electrified/rc2014-ym2149/example_template.kibot.yaml

# ATTENTION! THIS ISN'T A FULLY FUNCTIONAL EXAMPLE.
# You should take portions of this example and edit the options to make
# them suitable for your use.
# This file is useful to know all the available options.
# Try using `--quick-start` for a functional example.
kibot:
  version: 1

preflight:
  # Annotate PCB
  # Annotates the PCB according to physical coordinates.
  # This preflight modifies the PCB and schematic, use it only in revision control environments.
  # Used to assign references according to footprint coordinates.
  # The project must be fully annotated first .
  # [dict={}]  Options for the `annotate_pcb` preflight.
  annotate_pcb:
    top_main_axis: y
    top_main_ascending: true
    top_secondary_ascending: true
    top_start: 1
    bottom_main_axis: y
    bottom_main_ascending: true
    bottom_secondary_ascending: true
    bottom_start: 101
    use_position_of: 'footprint'
    grid: 1.0
  # Annotate Power
  # Annotates all power components.
  # This preflight modifies the schematic, use it only in revision control environments.
  # Used to solve ERC problems when using filters that remove power reference numbers .
  # [boolean=false] Enable this preflight.
  annotate_power: true
  # Check Fields
  # Checks to apply to the schematic fields.
  # You can define conditions that must be met by the fields.
  # The checks are applied to every component in the schematic.
  # When an error is hit execution is stopped.
  # One use is to check that all components are suitable for a temperature range.
  # In this case a field must declare the temperature range .
  # [dict|list(dict)=[]] One or more check rules.
  check_fields:
    - field: 'temperature'
      regex: '(-?\d+).+?(?:-?\d+).*'
      numeric_condition: '<='
      numeric_reference: -10
  # Check Zone Fills
  # Zones are filled before doing any operation involving PCB layers.
  # The original PCB remains unchanged. If you need to abort when the zone fill
  # creates significant changes to a layer use the CheckZoneFill internal template .
  # [boolean=false] Enable this preflight.
  check_zone_fills: true
  # Consolidate PCBs
  # Paste one or more PCBs into an existing PCB.
  # This is experimental and isn't intended for generating a PCB to work, just for 3D modeling and/or printing.
  # In the main PCB you just draw text boxes containing a name. Here you map this name to a PCB file name.
  # After executing this preflight the current PCB contains the references PCBs at the text boxes coordinates.
  # Only the top left corner of the text box is relevant.
  # An example can be found [here](https://github.com/INTI-CMNB/KiBot/tree/dev/docs/samples/Consolidate_PCBs)
  # .
  # [dict|list(dict)=[]] One or more PCBs to include.
  consolidate_pcbs: true
  # Draw Fancy Stackup
  # Draw the PCB stackup. Needs KiCad 7 or newer.
  # To specify the position and size of the drawing you can use two methods.
  # You can specify it using the *pos_x*, *pos_y*, *width* and *layer* options.
  # But you can also create a group called *kibot_fancy_stackup*. If you don't know how to
  # create a group consult :ref:`create_group`. After running this preflight the rectangle
  # will contain the stackup.
  # Note that the height is not determined by the group height, but by the number
  # of layers and spacing between layers. .
  # [boolean|dict=false] Use a boolean for simple cases or fine-tune its behavior.
  draw_fancy_stackup: true
  # Draw Stackup
  # Draw the PCB stackup. Needs KiCad 7 or newer.
  # To specify the position and size of the drawing you can use two methods.
  # You can specify it using the *pos_x*, *pos_y*, *width*, *height* and *layer* options.
  # But you can also create a group called *kibot_stackup*. If you don't know how to
  # create a group consult :ref:`create_group`. After running this preflight the rectangle
  # will contain the stackup .
  # [boolean|dict=false] Use a boolean for simple cases or fine-tune its behavior.
  draw_stackup: true
  # DRC
  # Runs the DRC (Distance Rules Check) to ensure we have a valid PCB.
  # You need a valid *fp-lib-table* installed. If not KiBot will try to temporarily install the template.
  # This is a replacement for the *run_drc* preflight that needs KiCad 8 or newer.
  # GUI exclusions and schematic parity are supported .
  # [boolean|dict=false] Use a boolean for simple cases or fine-tune its behavior.
  drc: true
  # ERC
  # Runs the ERC (Electrical Rules Check). To ensure the schematic is electrically correct.
  # You need a valid *sym-lib-table* installed. If not KiBot will try to temporarily install the template.
  # This is a replacement for the *run_erc* preflight that needs KiCad 8 or newer .
  # [boolean|dict=false] Use a boolean for simple cases or fine-tune its behavior.
  erc: true
  # ERC Warnings (**Deprecated**)
  # Option for `run_erc`. ERC warnings are considered errors.
  # Use the `warnings_as_errors` option from `run_erc`/`erc` instead .
  # [boolean=false] Enable this preflight.
  erc_warnings: false
  # Fill Zones
  # Fill all zones again and save the PCB .
  # [boolean=false] Enable this preflight.
  fill_zones: true
  # Filters
  # A list of entries to filter out ERC/DRC messages when using *run_erc*/*run_drc*.
  # Avoid using it with the new *erc* and *drc* preflights.
  # Note that ignored errors will become KiBot warnings (i.e. `(W058) ...`).
  # To farther ignore these warnings use the `filters` option in the `global` section .
  # [list(dict)=[]] One or more filters.
  filters:
    - filter: 'Filter description'
      error: '10'
      regex: 'Regular expression to match'
  # Ignore Unconnected (**Deprecated**)
  # Option for `run_drc`. Ignores the unconnected nets. Useful if you didn't finish the routing.
  # It will also ignore KiCad 6 warnings when using `run_drc`.
  # Use the `ignore_unconnected` option from `run_drc`/`drc` instead .
  # [boolean=false] Enable this preflight.
  ignore_unconnected: false
  # Include Table
  # Draws a table in the PCB from data in a CSV generated by an output. Needs KiCad 7 or newer.
  # To specify the position and size of the drawing create a group called *kibot_table_X* where
  # X should match the name of the output. If you don't know how to create a group consult
  # :ref:`create_group`. Consult the `group_name` option for details.
  # After running this preflight the rectangle will contain the table with the same name.
  # Only the width of the table is important, the height will be adjusted.
  # Important: This preflight assumes that a separated KiBot run generated the outputs
  # needed for the tables .
  # [boolean|dict=false] Use a boolean for simple cases or fine-tune its behavior.
  include_table: true
  # PCB Replace (**Deprecated**)
  # Replaces tags in the PCB. I.e. to insert the git hash or last revision date.
  # This is useful for KiCad 5, use `set_text_variables` when using KiCad 6.
  # This preflight modifies the PCB. Even when a back-up is done use it carefully .
  # [dict={}] Options for the `pcb_replace` preflight.
  pcb_replace:
    date_command: 'git log -1 --format="%as" -- "$KIBOT_PCB_NAME"'
    replace_tags:
      - tag: '@git_hash@'
        command: 'git log -1 --format="%h" "$KIBOT_PCB_NAME"'
        before: 'Git hash: <'
        after: '>'
  # Run DRC (**Deprecated for KiCad 8**)
  # Runs the DRC (Distance Rules Check) to ensure we have a valid PCB.
  # For KiCad 8 use *drc*
  # The report file name is controlled by the global output pattern (%i=drc %x=txt).
  # Note that the KiCad 6+ *Test for parity between PCB and schematic* option is not supported.
  # If you need to check the parity use the `update_xml` preflight.
  # KiCad 6 introduced `warnings` they are currently counted be the `unconnected` counter of KiBot.
  # This will change in the future.
  # If you use DRC exclusions please consult the `drc_exclusions_workaround` global option .
  # [boolean|dict=false] Use a boolean for simple cases or fine-tune its behavior.
  run_drc: true
  # Run ERC (**Deprecated for KiCad 8**)
  # Runs the ERC (Electrical Rules Check).
  # For KiCad 8 use *erc*
  # To ensure the schematic is electrically correct.
  # The report file name is controlled by the global output pattern (%i=erc %x=txt) .
  # [boolean|dict=false] Use a boolean for simple cases or fine-tune its behavior.
  run_erc: true
  # SCH Replace (**Deprecated**)
  # Replaces tags in the schematic. I.e. to insert the git hash or last revision date.
  # This is useful for KiCad 5, use `set_text_variables` when using KiCad 6.
  # This preflight modifies the schematics. Even when a back-up is done use it carefully .
  # [dict={}] Options for the `sch_replace` preflight.
  sch_replace:
    date_command: 'git log -1 --format="%as" -- "$KIBOT_SCH_NAME"'
    replace_tags:
      - tag: '@git_hash@'
        command: 'git log -1 --format="%h" "$KIBOT_SCH_NAME"'
        before: 'Git hash: <'
        after: '>'
  # Set Text Variables
  # Defines KiCad 6+ variables.
  # They are expanded using `${VARIABLE}`, and stored in the project file.
  # This preflight replaces `pcb_replace` and `sch_replace` when using KiCad 6 or newer.
  # The KiCad project file is modified.
  # Warning:     don't use `-s all` or this preflight will be skipped .
  # [dict|list(dict)=[]] One or more variable definition.
  set_text_variables:
    - name: 'git_hash'
      command: 'git log -1 --format="%h" "$KIBOT_PCB_NAME"'
      before: 'Git hash: <'
      after: '>'
  # Update Footprint
  # Updates footprints from the libs, you must provide one or more
  # references to be updated. This is useful to replace logos using freshly created versions .
  # [string|list(string)=''] {comma_sep} One or more component references.
  update_footprint: QR1,QR2
  # Update PCB Characteristics
  # Update the information in the Board Characteristics.
  # Starting with KiCad 7 you can paste a block containing board information using
  # Place* -> *Add Board Characteristics*. But this information is static, so if
  # you modify anything related to it the block will be obsolete.
  # This preflight tries to refresh the information .
  # [boolean=false] Enable this preflight.
  update_pcb_characteristics: true
  # Update QR
  # Update the QR codes.
  # Complements the `qr_lib` output.
  # The KiCad 6 files and the KiCad 5 PCB needs manual update, generating a new library isn't enough .
  # [boolean=false] Enable this preflight.
  update_qr: true
  # Update Stackup
  # Update the information in the Stackup Table.
  # Starting with KiCad 7 you can paste a block containing board information using
  # *Place* -> *Stackup Table*. But this information is static, so if
  # you modify anything related to it the block will be obsolete.
  # This preflight tries to refresh the information .
  # [boolean=false] Enable this preflight.
  update_stackup: true
  # Update XML
  # Update the XML version of the BoM (Bill of Materials).
  # To ensure our generated BoM is up to date.
  # Note that this isn't needed when using the internal BoM generator (`bom`).
  # You can compare the PCB and schematic netlists using it (KiCad 6 and 7 only) .
  # [boolean|dict=false] Use a boolean for simple cases or fine-tune its behavior.
  update_xml: true

outputs:
  # Blender Export:
  # Also renders the PCB with high-quality.
  # Needs KiCad 6 or newer.
  # This output is complex to setup and needs very big dependencies.
  # Please be patient when using it.
  # You need Blender with the pcb2blender plug-in installed.
  # Visit: [pcb2blender](https://github.com/30350n/pcb2blender).
  # You can just generate the exported PCB if no output is specified.
  # You can also export the PCB and render it at the same time
  - name: 'blender_export_example'
    comment: 'Exports the PCB in various 3D file formats.'
    type: 'blender_export'
    dir: 'Example/blender_export_dir'
    options:
      # [boolean=true] Add a default light when none specified.
      # The default light is located at (-size*3.33, size*3.33, size*5) where size is max(width, height) of the PCB
      add_default_light: true
      # [number=1.1] Value to multiply the Z axis coordinate after computing the automatically generated camera.
      # Used to avoid collision of the camera and the object
      auto_camera_z_axis_factor: 1.1
      # [dict={}] Options for the camera.
      # If none specified KiBot will create a suitable camera.
      # If no position is specified for the camera KiBot will look for a suitable position
      camera:
        # [number=-1] Minimum distance for objects to the camera. Any object closer than this distance won't be visible.
        # Only positive values have effect. A negative value has a special meaning.
        # For a camera with defined position, a negative value means to use Blender defaults (i.e. 0.1 m).
        # For cameras without position KiBot will ask Blender to compute its position and the use a clip
        # distance that is 1/10th of the Z distance
        clip_start: -1
        # [string=''] Name for the camera
        name: ''
        # [number|string=0] X position [m]. You can use `width`, `height` and `size` for PCB dimensions
        pos_x: 0
        # [number|string=0] Y position [m]. You can use `width`, `height` and `size` for PCB dimensions
        pos_y: 0
        # [number|string=0] Z position [m]. You can use `width`, `height` and `size` for PCB dimensions
        pos_z: 0
        # [string='perspective'] [perspective,orthographic,panoramic] Type of camera
        type: 'perspective'
      # [string=''] Default value for the `file_id` in the `point_of_view` options.
      # Use something like '_%03d' for animations
      default_file_id: ''
      # [boolean=false] When using the automatically generated camera and multiple points of view this option computes the camera
      # position just once. Suitable for videos
      fixed_auto_camera: false
      # [dict|list(dict)] Options for the light/s
      light:
        # [number=0] How powerful is the light. Using 0 for POINT and SUN KiBot will try to use something useful
        - energy: 0
          # [string=''] Name for the light
          name: ''
          # [number|string=0] X position [m]. You can use `width`, `height` and `size` for PCB dimensions
          pos_x: 0
          # [number|string=0] Y position [m]. You can use `width`, `height` and `size` for PCB dimensions
          pos_y: 0
          # [number|string=0] Z position [m]. You can use `width`, `height` and `size` for PCB dimensions
          pos_z: 0
          # [string='POINT'] [POINT,SUN,SPOT,HEMI,AREA] Type of light. SUN lights will illuminate more evenly
          type: 'POINT'
      # [dict|list(dict)] Outputs to generate in the same run
      outputs:
        # [string=''] Subdirectory for this output
        - dir: ''
          # [string='%f-%i%I%v.%x'] Name for the generated file (%i='3D_blender_$VIEW' %x=VARIABLE).
          # The extension is selected from the type. Affected by global options
          output: '%f-%i%I%v.%x'
          # [string='render'] [fbx,obj,x3d,gltf,stl,ply,blender,render] The format for the output.
          # The `render` type will generate a PNG image of the render result.
          # `fbx` is Kaydara's Filmbox, 'obj' is the Wavefront, 'x3d' is the new ISO/IEC standard
          # that replaced VRML, `gltf` is the standardized GL format, `stl` is the 3D printing
          # format, 'ply' is Polygon File Format (Stanford).
          # Note that some formats includes the light and camera and others are just the 3D model
          # (i.e. STL and PLY)
          type: 'render'
      # [string|dict={}] Options to export the PCB to Blender.
      # You can also specify the name of the output that generates the PCB3D file.
      # See the `PCB2Blender_2_1`, `PCB2Blender_2_7` and `PCB2Blender_2_1_haschtl` templates
      pcb3d:
        # [string|list(string)='_null'] Name of the filter to mark components as not fitted.
        # Is a short-cut to use for simple cases where a variant is an overkill.
        # Can be used to fine-tune a variant for a particular output that needs extra filtering done before the
        # variant
        dnf_filter: '_null'
        # [boolean=true] Downloads missing 3D models from KiCad git.
        # Only applies to models in KISYS3DMOD and KICAD6_3DMODEL_DIR.
        # They are downloaded to a temporal directory and discarded.
        # If you want to cache the downloaded files specify a directory using the
        # KIBOT_3D_MODELS environment variable
        download: true
        # [boolean=true] In addition to try to download the 3D models from KiCad git also try to get
        # them from LCSC database. In order to work you'll need to provide the LCSC
        # part number. The field containing the LCSC part number is defined by the
        # `field_lcsc_part` global variable
        download_lcsc: true
        # [string|list(string)='_null'] Name of the filter to exclude components from processing.
        # Is a short-cut to use for simple cases where a variant is an overkill.
        # Can be used to fine-tune a variant for a particular output that needs extra filtering done before the
        # variant
        exclude_filter: '_null'
        # [list(string)=[]] List of components to highlight. Ranges like *R5-R10* are supported
        highlight: []
        # [boolean=false] Highlight over the component (not under)
        highlight_on_top: false
        # [number=1.5] [0,1000] How much the highlight extends around the component [mm]
        highlight_padding: 1.5
        # [string='https://gitlab.com/kicad/libraries/kicad-packages3D/-/raw/master/'] Base URL for the KiCad 3D models
        kicad_3d_url: 'https://gitlab.com/kicad/libraries/kicad-packages3D/-/raw/master/'
        # [string=''] Text added to the end of the download URL.
        # Can be used to pass variables to the GET request, i.e. ?VAR1=VAL1&VAR2=VAL2
        kicad_3d_url_suffix: ''
        # [boolean=false] Used to exclude 3D models for components with 'virtual' attribute
        no_virtual: false
        # [string='%f-%i%I%v.%x'] Name for the generated PCB3D file (%i='blender_export' %x='pcb3d'). Affected by global options
        output: '%f-%i%I%v.%x'
        # [string|list(string)='_null'] Name of the filter to transform fields before applying other filters.
        # Is a short-cut to use for simple cases where a variant is an overkill.
        # Can be used to fine-tune a variant for a particular output that needs extra filtering done before the
        # variant
        pre_transform: '_null'
        # [list(string)|string='all'] [none,all,*] List of components to draw, can be also a string for `none` or `all`.
        # Ranges like *R5-R10* are supported.
        # Unlike the `pcbdraw` output, the default is `all`
        show_components: 'all'
        # [boolean=true] Solder the THT pads with heatsink fabrication attribute
        solder_join_on_heatsink: true
        # [boolean=true] Add solder paste only for the populated components.
        # Populated components are the ones listed in `show_components`
        solder_paste_for_populated: true
        # [string=''] Board variant to apply
        variant: ''
        # [string='2.7'] [2.1,2.1_haschtl,2.7] Variant of the format used
        version: '2.7'
      # [dict={}] Options to configure how Blender imports the PCB.
      # The default values are good for most cases
      pcb_import:
        # [boolean=true] Center the PCB at the coordinates origin
        center: true
        # [boolean=true] Import the components
        components: true
        # [boolean=true] Separate the sub-PCBs in separated 3D models
        cut_boards: true
        # [boolean=true] Create good looking materials
        enhance_materials: true
        # [boolean=true] Reuse materials
        merge_materials: true
        # [string='SMART'] [NONE,SMART,ALL] The plug-in can add nice looking solder joints.
        # This option controls if we add it for none, all or only for THT/SMD pads with solder paste
        solder_joints: 'SMART'
        # [boolean=true] Move the sub-PCBs to their relative position
        stack_boards: true
        # [number=1016.0] [508,2032] Texture density in dots per inch
        texture_dpi: 1016.0
      # [dict|list(dict)] How the object is viewed by the camera
      point_of_view:
        # [string=''] String to differentiate the name of this point of view.
        # When empty we use the `default_file_id` or the `view`
        - file_id: ''
          # [number=0] Angle to rotate the board in the X axis, positive is clockwise [degrees]
          rotate_x: 0
          # [number=0] Angle to rotate the board in the Y axis, positive is clockwise [degrees]
          rotate_y: 0
          # [number=0] Angle to rotate the board in the Z axis, positive is clockwise [degrees]
          rotate_z: 0
          # [number=1] [1,1000] Generate this amount of steps using the rotation angles as increments.
          # Use a value of 1 (default) to interpret the angles as absolute.
          # Used for animations. You should define the `default_file_id` to something like
          # '_%03d' to get the animation frames
          steps: 1
          # [string='top'] [top,bottom,front,rear,right,left,z,Z,y,Y,x,X] Point of view.
          # Compatible with `render_3d`
          view: 'top'
      # [dict={}] Controls how the render is done for the `render` output type
      render_options:
        # [boolean=false] When enabled the image will be post-processed to remove the empty space around the image.
        # In this mode the `background2` is changed to be the same as `background1`
        auto_crop: false
        # [string='#66667F'] First color for the background gradient
        background1: '#66667F'
        # [string='#CCCCE5'] Second color for the background gradient
        background2: '#CCCCE5'
        # `height` is an alias for `resolution_y`
        # [boolean=false] Used to disable the render denoiser on old hardware, or when the functionality isn't compiled.
        # Note that the impact in quality is huge, you should increase the amount of samples 10 times
        no_denoiser: false
        # [number=1280] Width of the image
        resolution_x: 1280
        # [number=720] Height of the image
        resolution_y: 720
        # [number=10] How many samples we create. Each sample is a raytracing render.
        # Use 1 for a raw preview, 10 for a draft and 100 or more for the final render
        samples: 10
        # [boolean=false] Make the background transparent
        transparent_background: false
        # `width` is an alias for `resolution_x`
  # BoardView:
  # This format allows simple pads and connections navigation, mainly for circuit debug.
  # The output can be loaded using Open Board View (https://openboardview.org/)
  - name: 'boardview_example'
    comment: 'Exports the PCB in board view format.'
    type: 'boardview'
    dir: 'Example/boardview_dir'
    options:
      # [string|list(string)='_null'] Name of the filter to mark components as not fitted.
      # Is a short-cut to use for simple cases where a variant is an overkill.
      # Can be used to fine-tune a variant for a particular output that needs extra filtering done before the
      # variant
      dnf_filter: '_null'
      # [string|list(string)='_null'] Name of the filter to exclude components from processing.
      # Is a short-cut to use for simple cases where a variant is an overkill.
      # Can be used to fine-tune a variant for a particular output that needs extra filtering done before the
      # variant
      exclude_filter: '_null'
      # [string='BRD'] [BRD,BVR,OBDATA] Format used for the generated file. The BVR file format is bigger but keeps
      # more information, like alphanumeric pin names.
      # OBDATA is the OpenBoardData format. You can include the manufacturer part number defining the global
      # `field_part_number` variable. Excluded and not fitted components are marked with `-` status
      format: 'BRD'
      # [string='%f-%i%I%v.%x'] Filename for the output (%i=boardview, %x=brd/brv). Affected by global options
      output: '%f-%i%I%v.%x'
      # [string|list(string)='_null'] Name of the filter to transform fields before applying other filters.
      # Is a short-cut to use for simple cases where a variant is an overkill.
      # Can be used to fine-tune a variant for a particular output that needs extra filtering done before the
      # variant
      pre_transform: '_null'
      # [boolean=true] Sort components by reference. Disable this option to get a file closer to what
      # kicad-boardview generates
      sorted: true
      # [string=''] Board variant to apply.
      # Used for sub-PCBs
      variant: ''
  # BoM (Bill of Materials):
  # This output can generate XYRS files (pick and place files).
  # You can import the options used in the KiCad internal BoM, consult :ref:`bom_kicad_options`.
  # Is compatible with KiBoM, but doesn't need to update the XML netlist because the components
  # are loaded from the schematic.
  # Important differences with KiBoM output:
  # - All options are in the main `options` section, not in `conf` subsection.
  # - The `Component` column is named `Row` and works just like any other column.
  - name: 'bom_example'
    comment: 'Used to generate the BoM in CSV, HTML, TSV, TXT, XML or XLSX format using the internal BoM.'
    type: 'bom'
    dir: 'Example/bom_dir'
    options:
      # [list(dict)=[]] Add components from other projects.
      # You can use CSV files, the first row must contain the names of the fields.
      # The `Reference` and `Value` are mandatory, in most cases `Part` is also needed.
      # The `Part` column should contain the name/type of the component. This is important for
      # passive components (R, L, C, etc.). If this information isn't available consider
      # configuring the grouping to exclude the `Part`
      aggregate:
        # [string=','] Delimiter used for CSV files
        - delimiter: ','
          # [string=''] Name of the schematic to aggregate
          file: 'another_schematic.kicad_sch'
          # [string=''] Name to identify this source. If empty we use the name of the schematic
          name: ''
          # [number=1] Number of boards to build (components multiplier). Use negative to subtract
          number: 1
          # [string=''] A prefix to add to all the references from this project
          ref_id: ''
      # [boolean=true] Always use positive values for the footprint rotation
      angle_positive: true
      # [boolean=false] Use negative X coordinates for footprints on bottom layer (for XYRS)
      bottom_negative_x: false
      # [list(dict)|list(string)=computed for your project] List of columns to display.
      # One entry can be just the name of the field (a string).
      # If you want to import the columns used in KiCad internal BoM tool add an entry `_kicad_bom_fields`,
      # this will be replaced by the list from KiCad.
      # In addition to all user defined fields you have various special columns, consult :ref:`bom_columns`
      columns:
        # [string=''] Used as explanation for this column. The XLSX output uses it
        - comment: ''
          # [string=''] Name of the field to use for this column.
          # Use `_field_lcsc_part` to get the value defined in the global options
          field: 'Row'
          # [list(dict)|list(string)|string=''] List of fields to join to this column
          join:
            # [string=''] {no_case} Name of the field
            - field: 'Voltage'
              # [string=''] Text to use instead of a field. This option is incompatible with the `field` option.
              # Any space to separate it should be added in the text.
              # Use \n for newline and \t for tab
              text: ''
              # [string=''] Text to add after the field content. Will be added only if the field isn't empty.
              # Any space to separate it should be added in the text.
              # Use \n for newline and \t for tab
              text_after: ''
              # [string=''] Text to add before the field content. Will be added only if the field isn't empty.
              # Any space to separate it should be added in the text.
              # Use \n for newline and \t for tab
              text_before: ''
          # [number=0] Used to group columns. The XLSX output uses it to collapse columns
          level: 0
          # [string=''] Name to display in the header. The field is used when empty
          name: 'Line'
      # [list(list(string))] A series of values which are considered to be equivalent for the part name.
      # Each entry is a list of equivalen names. Example: ['c', 'c_small', 'cap' ]
      # will ensure the equivalent capacitor symbols can be grouped together.
      # If empty the following aliases are used:
      # - ['r', 'r_small', 'res', 'resistor']
      # - ['l', 'l_small', 'inductor']
      # - ['c', 'c_small', 'cap', 'capacitor']
      # - ['sw', 'switch']
      # - ['zener', 'zenersmall']
      # - ['d', 'diode', 'd_small']
      component_aliases: [['r', 'r_small', 'res', 'resistor'], ['l', 'l_small', 'inductor'], ['c', 'c_small', 'cap', 'capacitor'], ['sw', 'switch'], ['zener', 'zenersmall'], ['d', 'diode', 'd_small']]
      # [list(dict)|list(string)=[]] List of columns to add to the global section of the cost.
      # Can be just the name of the field
      cost_extra_columns:
        # [string=''] Used as explanation for this column. The XLSX output uses it
        - comment: ''
          # [string=''] Name of the field to use for this column.
          # Use `_field_lcsc_part` to get the value defined in the global options
          field: 'Row'
          # [list(dict)|list(string)|string=''] List of fields to join to this column
          join:
            # [string=''] {no_case} Name of the field
            - field: 'Voltage'
              # [string=''] Text to use instead of a field. This option is incompatible with the `field` option.
              # Any space to separate it should be added in the text.
              # Use \n for newline and \t for tab
              text: ''
              # [string=''] Text to add after the field content. Will be added only if the field isn't empty.
              # Any space to separate it should be added in the text.
              # Use \n for newline and \t for tab
              text_after: ''
              # [string=''] Text to add before the field content. Will be added only if the field isn't empty.
              # Any space to separate it should be added in the text.
              # Use \n for newline and \t for tab
              text_before: ''
          # [number=0] Used to group columns. The XLSX output uses it to collapse columns
          level: 0
          # [string=''] Name to display in the header. The field is used when empty
          name: 'Line'
      # [boolean=false] Show the stats about how many of the components are SMD/THT. You must provide the PCB
      count_smd_tht: false
      # [dict={}] Options for the CSV, TXT and TSV formats
      csv:
        # [boolean=false] Hide the header line (names of the columns)
        hide_header: false
        # [boolean=false] Hide project information
        hide_pcb_info: false
        # [boolean=false] Hide statistics information
        hide_stats_info: false
        # [boolean=true] Don't remove line breaks in field values
        keep_line_breaks: true
        # [boolean=true] Don't remove tabs in field values
        keep_tabs: true
        # [boolean=false] Enclose all values using double quotes
        quote_all: false
        # [string=','] CSV Separator. TXT and TSV always use tab as delimiter.
        # Only one character can be specified
        separator: ','
        # [string='"'] Character used to delimite strings
        string_delimiter: '"'
      # [string|list(string)=[]] {comma_sep} Include this distributors list. Default is all the available
      distributors: []
      # [string|list(string)='_kibom_dnc_CONFIG_FIELD'] Name of the filter to mark components as 'Do Not Change'.
      # The default filter marks components with a DNC value or DNC in the Config field.
      # This option is for simple cases, consider using a full variant for complex cases
      dnc_filter: '_kibom_dnc_CONFIG_FIELD'
      # [string|list(string)='_kibom_dnf_CONFIG_FIELD'] Name of the filter to mark components as 'Do Not Fit'.
      # The default filter marks components with a DNF value or DNF in the Config field.
      # This option is for simple cases, consider using a full variant for complex cases
      dnf_filter: '_kibom_dnf_CONFIG_FIELD'
      # [string|list(string)='_mechanical'] Name of the filter to exclude components from BoM processing.
      # The default filter (built-in filter '_mechanical') excludes test points, fiducial marks, mounting holes, etc.
      # Please consult the built-in filters explanation to fully understand what is excluded by default.
      # This option is for simple cases, consider using a full variant for complex cases
      exclude_filter: '_mechanical'
      # [boolean=false] Exclude components marked with *Exclude from BOM* in the PCB.
      # This is a KiCad 6 option
      exclude_marked_in_pcb: false
      # [boolean=true] Exclude components marked with *Exclude from bill of materials* in the schematic.
      # This is a KiCad 6 option
      exclude_marked_in_sch: true
      # [boolean=true] Expand KiCad 6 text variables after applying all filters and variants.
      # This is done using a **_expand_text_vars** filter.
      # If you need to customize the filter, or apply it before, you can disable this option and
      # add a custom filter to the filter chain
      expand_text_vars: true
      # [string='config'] {no_case} Field name used for internal filters (not for variants)
      fit_field: 'config'
      # [string|list(string)='no,yes'] {comma_sep} {L:2} Values for the `Footprint Populate` column
      footprint_populate_values: 'no,yes'
      # [string|list(string)='SMD,THT,VIRTUAL'] {comma_sep} {L:3} Values for the `Footprint Type` column
      footprint_type_values: 'SMD,THT,VIRTUAL'
      # [string='Auto'] [HTML,CSV,TXT,TSV,XML,XLSX,HRTXT,KICAD,Auto] format for the BoM.
      # `Auto` defaults to CSV or a guess according to the options.
      # HRTXT stands for Human Readable TeXT.
      # KICAD is used to get the options from KiCad project. In KiCad you can configure CSV like options
      format: 'Auto'
      # [boolean=true] Connectors with the same footprints will be grouped together, independent of the name of the connector
      group_connectors: true
      # [list(string)] {no_case} List of fields used for sorting individual components into groups.
      # Components which match (comparing *all* fields) will be grouped together.
      # Field names are case-insensitive.
      # For empty fields the behavior is defined by the `group_fields_fallbacks`, `merge_blank_fields` and
      # `merge_both_blank` options.
      # Note that for resistors, capacitors and inductors the _Value_ field is parsed and qualifiers, like
      # tolerance, are discarded. Please use a separated field and disable `merge_blank_fields` if this
      # information is important. You can also disable `parse_value`.
      # When using `_kicad_bom_fields` in the `columns` you should use `[]` for this value, so the fields
      # selected in KiCad are used.
      # If empty: ['Part', 'Part Lib', 'Value', 'Footprint', 'Footprint Lib',
      #            'Voltage', 'Tolerance', 'Current', 'Power'] is used
      group_fields: ['part', 'part lib', 'value', 'footprint', 'footprint lib', 'voltage', 'tolerance', 'current', 'power']
      # [list(string)=[]] {no_case} List of fields to be used when the fields in `group_fields` are empty.
      # The first field in this list is the fallback for the first in `group_fields`, and so on
      group_fields_fallbacks: []
      # [boolean=false] Enable it to group fitted and not fitted components together. This is how KiCad's internal BoM behaves
      group_not_fitted: false
      # [dict={}] Options for the HRTXT formats
      hrtxt:
        # [string='-'] Separator between the header and the data
        header_sep: '-'
        # [boolean=false] Hide the header line (names of the columns)
        hide_header: false
        # [boolean=false] Hide project information
        hide_pcb_info: false
        # [boolean=false] Hide statistics information
        hide_stats_info: false
        # [string='left'] [left,right,center] Text justification
        justify: 'left'
        # [string='I'] Column Separator
        separator: 'I'
      # [dict={}] Options for the HTML format
      html:
        # [boolean=true] Use colors to show the field type
        col_colors: true
        # [string=''] {no_case} Column with links to the datasheet
        datasheet_as_link: ''
        # [string|list(string)=''] {no_case} Column/s containing Digi-Key part numbers, will be linked to web page
        digikey_link: ''
        # [string|list(string)=''] Information to put after the title and before the pcb and stats info
        extra_info: ''
        # [boolean=true] Generate a separated section for DNF (Do Not Fit) components
        generate_dnf: true
        # [boolean=false] Hide project information
        hide_pcb_info: false
        # [boolean=false] Hide statistics information
        hide_stats_info: false
        # [boolean=true] Use a color for empty cells. Applies only when `col_colors` is `true`
        highlight_empty: true
        # [boolean|string|list(string)=''] {no_case} Column/s containing LCSC part numbers, will be linked to web page.
        # Use **true** to copy the value indicated by the `field_lcsc_part` global option
        lcsc_link: ''
        # [string|boolean=''] PNG/SVG file to use as logo, use false to remove.
        # Note that when using an SVG this is first converted to a PNG using `logo_width`
        logo: ''
        # [number=370] Used when the logo is an SVG image. This width is used to render the SVG image
        logo_width: 370
        # [string|list(string)=''] {no_case} Column/s containing Mouser part numbers, will be linked to web page
        mouser_link: ''
        # [list(dict)=[]] Used to highlight rows using filters. Rows that match a filter can be colored.
        # Note that these rows won't have colored columns
        row_colors:
          # [string='#FF8080'] Color used for this category
          - color: '#FF8080'
            # [string=''] A description for this color, must be filled
            description: "Components that can't be replaced"
            # [string|list(string)='_none'] Name of the filter to match.
            # Be careful because this filter should be coherent with the grouping fields.
            # KiBot will assume that all the components grouped in the same group will
            # return the same value when applying this filter
            filter: '_none'
        # [string='modern-blue'] Page style. Internal styles: modern-blue, modern-green, modern-red and classic.
        # Or you can provide a CSS file name. Please use .css as file extension.
        style: 'modern-blue'
        # [string='KiBot Bill of Materials'] BoM title
        title: 'KiBot Bill of Materials'
      # [boolean=true] Exclude DNF (Do Not Fit) components
      ignore_dnf: true
      # [boolean=true] Component quantities are always expressed as integers. Using the ceil() function
      int_qtys: true
      # [string='global'] [global,yes,no] What we do with the KiCad DNP flag.
      # `global` means we apply the `kicad_dnp_applied` global option.
      # `yes` means we always remove DNP components.
      # `no` means we ignore the DNP flag and let filters do its work
      kicad_dnp_applied: 'global'
      # [boolean=true] Component groups with blank fields will be merged into the most compatible group, where possible
      merge_blank_fields: true
      # [boolean=true] When creating groups two components with empty/missing field will be interpreted as with the same value
      merge_both_blank: true
      # [list(string)=computed for your project] {no_case} List of fields where we tolerate conflicts.
      # Use it to avoid undesired warnings.
      # By default the field indicated in `fit_field`, the field used for variants and
      # the field `part` are excluded
      no_conflict: ['Config', 'Part']
      # [string|list(string)=[]] {comma_sep} Exclude this distributors list.
      # They are removed after computing `distributors`
      no_distributors: []
      # [boolean=false] When normalizing values use the locale decimal point
      normalize_locale: false
      # [boolean=false] Try to normalize the R, L and C values, producing uniform units and prefixes
      normalize_values: false
      # [number=1] Number of boards to build (components multiplier)
      number: 1
      # [string='%f-%i%I%v.%x'] filename for the output (%i=bom). The extension depends on the selected format.
      # In the case of the **KICAD** format the extension comes from the name you selected in KiCad's
      # internal BoM. Affected by global options
      output: '%f-%i%I%v.%x'
      # [boolean=true] Parse the `Value` field so things like *1k* and *1000* are interpreted as equal.
      # Note that this implies that *1k 1%* is the same as *1k 5%*. If you really need to group using the
      # extra information split it in separated fields, add the fields to `group_fields` and disable
      # `merge_blank_fields`
      parse_value: true
      # [string|list(string)='_null'] Name of the filter to transform fields before applying other filters.
      # This option is for simple cases, consider using a full variant for complex cases
      pre_transform: '_null'
      # [string=''] A prefix to add to all the references from this project. Used for multiple projects
      ref_id: ''
      # [string='-'] Separator used for ranges in the list of references. Used when `use_alt` is enabled.
      # Ignored when using the KICAD format
      ref_range_separator: '-'
      # [string=' '] Separator used for the list of references. Ignored when using the KICAD format
      ref_separator: ' '
      # [number=4] Number of digits for mantissa part of coordinates ('Footprint X', 'Footprint Y', 'Footprint X-Size',
      # 'Footprint Y-Size' and 'Footprint Rot' columns) (0 is auto)
      right_digits: 4
      # [boolean=true] Sort in ascending order
      sort_ascending: true
      # [string|list(string)='Reference'] {no_case} Field or fields used for the `field` `sort_style`
      sort_field: 'Reference'
      # [string='type_value'] [type_value,type_value_ref,ref,kicad_bom,field] Sorting criteria.
      # - type_value: component kind (reference prefix), then by value
      # - type_value_ref: like *type_value* but use the reference when we don't have a value
      # - ref: by reference
      # - kicad_bom: according to the options of the KiCad BoM tool
      # - field: using the `sort_field` field/s
      sort_style: 'type_value'
      # [boolean=false] Generate the `Source BoM` column using the reference ID instead of the project name
      source_by_id: false
      # [string='millimeters'] [millimeters,inches,mils] Units used for the positions ('Footprint X', 'Footprint Y', 'Footprint X-Size' and
      # 'Footprint Y-Size' columns).
      # Affected by global options
      units: 'millimeters'
      # [boolean=false] Print grouped references in the alternate compressed style eg: R1-R7,R18.
      # Ignored when using the KICAD format
      use_alt: false
      # [boolean=true] Use the auxiliary axis as origin for coordinates (KiCad default) (for XYRS)
      use_aux_axis_as_origin: true
      # `use_ref_ranges` is an alias for `use_alt`
      # [string='_kibom_simple'] Board variant, used to determine which components are output to the BoM.
      # The `_kibom_simple` variant is a KiBoM variant without any filters and it provides some basic
      # compatibility with KiBoM. Note that this output has default filters that behaves like KiBoM.
      # The combination between the default for this option and the defaults for the filters provides
      # a behavior that mimics KiBoM default behavior
      variant: '_kibom_simple'
      # [dict={}] Options for the XLSX format
      xlsx:
        # [boolean=true] Use colors to show the field type
        col_colors: true
        # [string=''] {no_case} Column with links to the datasheet
        datasheet_as_link: ''
        # [string|list(string)=''] {no_case} Column/s containing Digi-Key part numbers, will be linked to web page
        digikey_link: ''
        # [string|list(string)=''] Information to put after the title and before the pcb and stats info
        extra_info: ''
        # [boolean=true] Generate a separated section for DNF (Do Not Fit) components
        generate_dnf: true
        # [boolean=false] Hide project information
        hide_pcb_info: false
        # [boolean=false] Hide statistics information
        hide_stats_info: false
        # [boolean=true] Use a color for empty cells. Applies only when `col_colors` is `true`
        highlight_empty: true
        # [boolean=false] Enable KiCost worksheet creation.
        # Note: an example of how to use it on CI/CD can be found [here](https://github.com/set-soft/kicost_ci_test)
        kicost: false
        # [string|list(string)=''] {comma_sep} List of KiCost APIs to disable
        kicost_api_disable: ''
        # [string|list(string)=''] {comma_sep} List of KiCost APIs to enable
        kicost_api_enable: ''
        # [string=''] KiCost configuration file. It contains the keys for the different distributors APIs.
        # The regular KiCost config is used when empty.
        # Important for CI/CD environments: avoid exposing your API secrets!
        # To understand how to achieve this, and also how to make use of the cache please visit the
        # [kicost_ci_test](https://github.com/set-soft/kicost_ci_test) repo
        kicost_config: ''
        # [boolean=false] Used to add a column with the distributor's description. So you can check this is the right component
        kicost_dist_desc: false
        # [boolean|string|list(string)=''] {no_case} Column/s containing LCSC part numbers, will be linked to web page.
        # Use **true** to copy the value indicated by the `field_lcsc_part` global option
        lcsc_link: ''
        # [string|boolean=''] PNG/SVG file to use as logo, use false to remove.
        # Note that when using an SVG this is first converted to a PNG using `logo_width`
        logo: ''
        # [number=2] Scaling factor for the logo. Note that this value isn't honored by all spreadsheet software
        logo_scale: 2
        # [number=370] Used when the logo is an SVG image. This width is used to render the SVG image
        logo_width: 370
        # [number=60] [20,999] Maximum column width (characters)
        max_col_width: 60
        # [string|list(string)=''] {no_case} Column/s containing Mouser part numbers, will be linked to web page
        mouser_link: ''
        # [list(dict)=[]] Used to highlight rows using filters. Rows that match a filter can be colored.
        # Note that these rows won't have colored columns
        row_colors:
          # [string='#FF8080'] Color used for this category
          - color: '#FF8080'
            # [string=''] A description for this color, must be filled
            description: "Components that can't be replaced"
            # [string|list(string)='_none'] Name of the filter to match.
            # Be careful because this filter should be coherent with the grouping fields.
            # KiBot will assume that all the components grouped in the same group will
            # return the same value when applying this filter
            filter: '_none'
        # [boolean=false] Enable Specs worksheet creation. Contains specifications for the components.
        # Works with only some KiCost APIs
        specs: false
        # [list(dict)|list(string)=[]] Which columns are included in the Specs worksheet. Use `References` for the
        # references, 'Row' for the order and 'Sep' to separate groups at the same level. By default all are included.
        # Column names are distributor specific, the following aren't: '_desc', '_value', '_tolerance', '_footprint',
        # '_power', '_current', '_voltage', '_frequency', '_temp_coeff', '_manf', '_size'.
        # Note that an empty list means all available specs, use `specs` options to disable it
        specs_columns:
          # [string=''] Used as explanation for this column. The XLSX output uses it
          - comment: ''
            # [string=''] Name of the field to use for this column.
            # Use `_field_lcsc_part` to get the value defined in the global options
            field: 'Row'
            # [list(dict)|list(string)|string=''] List of fields to join to this column
            join:
              # [string=''] {no_case} Name of the field
              - field: 'Voltage'
                # [string=''] Text to use instead of a field. This option is incompatible with the `field` option.
                # Any space to separate it should be added in the text.
                # Use \n for newline and \t for tab
                text: ''
                # [string=''] Text to add after the field content. Will be added only if the field isn't empty.
                # Any space to separate it should be added in the text.
                # Use \n for newline and \t for tab
                text_after: ''
                # [string=''] Text to add before the field content. Will be added only if the field isn't empty.
                # Any space to separate it should be added in the text.
                # Use \n for newline and \t for tab
                text_before: ''
            # [number=0] Used to group columns. The XLSX output uses it to collapse columns
            level: 0
            # [string=''] Name to display in the header. The field is used when empty
            name: 'Line'
        # [string='modern-blue'] Head style: modern-blue, modern-green, modern-red and classic
        style: 'modern-blue'
        # [string='KiBot Bill of Materials'] BoM title
        title: 'KiBot Bill of Materials'
  # Archiver (files compressor):
  # This is used to generate groups of files in compressed file format.
  - name: 'compress_example'
    comment: 'Generates a compressed file containing output files.'
    type: 'compress'
    dir: 'Example/compress_dir'
    options:
      # [string='auto'] [auto,stored,deflated,bzip2,lzma] Compression algorithm. Use auto to let KiBot select a suitable one
      compression: 'auto'
      # [list(dict)=[]] Which files will be included
      files:
        # [string=''] Destination directory inside the archive, empty means the same of the file
        - dest: ''
          # [string='.*'] A regular expression that source files must match
          filter: '.*'
          # [boolean=false] Use the current working directory instead of the dir specified by `-d`
          from_cwd: false
          # [string=''] Collect files from the selected output.
          # When used the `source` option is ignored
          from_output: ''
          # [boolean=false] Use the current directory specified by the output instead of the dir specified by `-d`.
          # Note that it only applies when using `from_output` and no `dest` is specified.
          # It has more prescedence than `from_cwd`
          from_output_dir: false
          # [string='*'] File names to add, wildcards allowed. Use ** for recursive match.
          # By default this pattern is applied to the output dir specified with `-d` command line option.
          # See the `from_cwd` and `from_output_dir` options
          source: '*'
      # [boolean=true] Store the file pointed by symlinks, not the symlink
      follow_links: true
      # [string='ZIP'] [ZIP,TAR,RAR] Output file format
      format: 'ZIP'
      # [boolean=false] Move the files to the archive. In other words: remove the files after adding them to the archive
      move_files: false
      # [string='%f-%i%I%v.%x'] Name for the generated archive (%i=name of the output %x=according to format). Affected by global options
      output: '%f-%i%I%v.%x'
      # `remove_files` is an alias for `move_files`
      # [boolean=false] Skip outputs with `run_by_default: false`
      skip_not_run: false
  # Files copier:
  # Useful when an external tool is used to compress the output directory.
  # Note that you can use the `compress` output to create archives
  - name: 'copy_files_example'
    comment: 'Used to copy files to the output directory.'
    type: 'copy_files'
    dir: 'Example/copy_files_dir'
    options:
      # [string|list(string)='_null'] Name of the filter to mark components as not fitted.
      # Is a short-cut to use for simple cases where a variant is an overkill.
      # Can be used to fine-tune a variant for a particular output that needs extra filtering done before the
      # variant
      dnf_filter: '_null'
      # [boolean=true] Downloads missing 3D models from KiCad git.
      # Only applies to models in KISYS3DMOD and KICAD6_3DMODEL_DIR.
      # They are downloaded to a temporal directory and discarded.
      # If you want to cache the downloaded files specify a directory using the
      # KIBOT_3D_MODELS environment variable
      download: true
      # [boolean=true] In addition to try to download the 3D models from KiCad git also try to get
      # them from LCSC database. In order to work you'll need to provide the LCSC
      # part number. The field containing the LCSC part number is defined by the
      # `field_lcsc_part` global variable
      download_lcsc: true
      # [string|list(string)='_null'] Name of the filter to exclude components from processing.
      # Is a short-cut to use for simple cases where a variant is an overkill.
      # Can be used to fine-tune a variant for a particular output that needs extra filtering done before the
      # variant
      exclude_filter: '_null'
      # [list(dict)=[]] Which files will be included
      files:
        # [string=''] Destination directory inside the output dir, empty means the same of the file
        # relative to the source directory.
        # Note that when you specify a name here files are copied to this destination
        # without creating subdirs. The `project` mode is an exception.
        # For the `3d_models` type you can use DIR+ to create subdirs under DIR
        - dest: ''
          # [string='.*'] A regular expression that source files must match.
          # Not used for the `project` mode
          filter: '.*'
          # [boolean=false] Only usable for the `3d_models` mode.
          # Save a PCB copy modified to use the copied 3D models.
          # You don't need to specify it for `project` mode
          save_pcb: false
          # [string='*'] For the `files` and `out_files` mode this is th file names to add,
          # wildcards allowed. Use ** for recursive match.
          # For the `output` mode this is the name of the output.
          # For the `3d_models` is a pattern to match the name of the 3D models extracted from the PCB.
          # Not used for the `project` mode
          source: '*'
          # [string='files'] [files,out_files,output,3d_models,project] From where do we get the files to be copied.
          # - `files`: files relative to the current working directory.
          # - `out_files`: files relative to output dir specified with `-d` command line option.
          # - `output`: files generated by the output specified by `source`.
          # - `3d_models`: 3D models used in the project.
          # - `project`: schematic, PCB, footprints, symbols, 3D models and project files (KiCad 6+)
          source_type: 'files'
      # [boolean=true] Store the file pointed by symlinks, not the symlink
      follow_links: true
      # [string='https://gitlab.com/kicad/libraries/kicad-packages3D/-/raw/master/'] Base URL for the KiCad 3D models
      kicad_3d_url: 'https://gitlab.com/kicad/libraries/kicad-packages3D/-/raw/master/'
      # [string=''] Text added to the end of the download URL.
      # Can be used to pass variables to the GET request, i.e. ?VAR1=VAL1&VAR2=VAL2
      kicad_3d_url_suffix: ''
      # [boolean=false] Create symlinks instead of copying files
      link_no_copy: false
      # [boolean=false] Used to exclude 3D models for components with 'virtual' attribute
      no_virtual: false
      # [string|list(string)='_null'] Name of the filter to transform fields before applying other filters.
      # Is a short-cut to use for simple cases where a variant is an overkill.
      # Can be used to fine-tune a variant for a particular output that needs extra filtering done before the
      # variant
      pre_transform: '_null'
      # [string=''] Board variant to apply
      variant: ''
  # Diff:
  # Recursive git submodules aren't supported (submodules inside submodules)
  - name: 'diff_example'
    comment: 'Generates a PDF with the differences between two PCBs or schematics.'
    type: 'diff'
    dir: 'Example/diff_dir'
    options:
      # [boolean=false] When enabled we create a symlink to the output file with a name that contains the
      # git hashes involved in the comparison. If you plan to compress the output don't
      # forget to disable the `follow_links` option
      add_link_id: false
      # [boolean=false] Always fail if the old/new file doesn't exist. Currently we don't fail if they are from a repo.
      # So if you refer to a repo point where the file wasn't created KiBot will use an empty file.
      # Enabling this option KiBot will report an error
      always_fail_if_missing: false
      # [string=''] Directory to cache the intermediate files. Leave it blank to disable the cache
      cache_dir: ''
      # [string='#00FF00'] Color used for the added stuff in the '2color' mode
      color_added: '#00FF00'
      # [string='#FF0000'] Color used for the removed stuff in the '2color' mode
      color_removed: '#FF0000'
      # [boolean=false] Modifies the behavior of `add_link_id` to create a copy of the file instead of a
      # symlink. Useful for some Windows setups
      copy_instead_of_link: false
      # [string='red_green'] [red_green,stats,2color] In the `red_green` mode added stuff is green and red when removed.
      # The `stats` mode is used to measure the amount of difference. In this mode all
      # changes are red, but you can abort if the difference is bigger than certain threshold.
      # The '2color' mode is like 'red_green', but you can customize the colors
      diff_mode: 'red_green'
      # [string|list(string)='_null'] Name of the filter to mark components as not fitted.
      # Is a short-cut to use for simple cases where a variant is an overkill.
      # Can be used to fine-tune a variant for a particular output that needs extra filtering done before the
      # variant
      dnf_filter: '_null'
      # [string|list(string)='_null'] Name of the filter to exclude components from processing.
      # Is a short-cut to use for simple cases where a variant is an overkill.
      # Can be used to fine-tune a variant for a particular output that needs extra filtering done before the
      # variant
      exclude_filter: '_null'
      # [boolean=false] When `old_type` and/or `new_type` are `git` KiBot will checkout the indicated point.
      # Before doing it KiBot will stash any change. Under some circumstances git could fail
      # to do a checkout, even after stashing, this option can workaround the problem.
      # Note that using it you could potentially lose modified files. For more information
      # read https://stackoverflow.com/questions/1248029/git-pull-error-entry-foo-not-uptodate-cannot-merge
      force_checkout: false
      # [number=5] [0,100] Color tolerance (fuzzyness) for the `stats` mode
      fuzz: 5
      # [string|list(string)] The file you want to compare. Leave it blank for the current PCB/SCH.
      # A list is accepted only for the `multivar` type. Consult the `old` option for more information
      new: ''
      # [string='current'] [git,file,output,multivar,current] How to interpret the `new` name. Use `git` for a git hash, branch, etc.
      # Use `current` for the currently loaded PCB/Schematic.
      # Use `file` for a file name. Use `output` to specify the name of a `pcb_variant`/`sch_variant` output.
      # Use `multivar` to compare a set of variants, in this mode `new` is the list of outputs for the variants.
      # This is an extension of the `output` mode.
      # If `old` is also `multivar` then it becomes the reference, otherwise we compare using pairs of variants
      new_type: 'current'
      # [string='HEAD'] Reference file. When using git use `HEAD` to refer to the last commit.
      # Use `HEAD~` to refer the previous to the last commit.
      # As `HEAD` is for the whole repo you can use `KIBOT_LAST-n` to make
      # reference to the changes in the PCB/SCH. The `n` value is how many
      # changes in the history you want to go back. A 0 is the same as `HEAD`,
      # a 1 means the last time the PCB/SCH was changed, etc.
      # Use `KIBOT_TAG-n` to search for the last tag skipping `n` tags.
      # Important: when using the `checkout` GitHub action you just get the
      # last commit. To clone the full repo use `fetch-depth: '0'`
      old: 'HEAD'
      # [string='git'] [git,file,output,multivar] How to interpret the `old` name. Use `git` for a git hash, branch, etc.
      # Use `file` for a file name. Use `output` to specify the name of a `pcb_variant`/`sch_variant` output.
      # Use `multivar` to specify a reference file when `new_type` is also `multivar`
      old_type: 'git'
      # [boolean=false] Only include the pages with differences in the output PDF.
      # Note that when no differences are found we get a page saying *No diff*
      only_different: false
      # [boolean=false] Compare only the main schematic page (root page).
      # Warning: Make sure this page is the page **1** of your schematic
      only_first_sch_page: false
      # [string='%f-%i%I%v.%x'] Filename for the output (%i=diff_pcb/diff_sch, %x=pdf). Affected by global options
      output: '%f-%i%I%v.%x'
      # [boolean=true] Compare the PCB, otherwise compare the schematic
      pcb: true
      # [string|list(string)='_null'] Name of the filter to transform fields before applying other filters.
      # Is a short-cut to use for simple cases where a variant is an overkill.
      # Can be used to fine-tune a variant for a particular output that needs extra filtering done before the
      # variant
      pre_transform: '_null'
      # [number=0] [0,1000000] Error threshold for the `stats` mode, 0 is no error. When specified a
      # difference bigger than the indicated value will make the diff fail.
      # KiBot will return error level 29 and the diff generation will be aborted
      threshold: 0
      # [boolean=false] When creating the link name of an output file related to a variant use the variant
      # `file_id` instead of its name
      use_file_id: false
      # [string=''] Board variant to apply
      variant: ''
      # [string='global'] [global,fill,unfill,none] How to handle PCB zones. The default is *global* and means that we
      # fill zones if the *check_zone_fills* preflight is enabled. The *fill* option always forces
      # a refill, *unfill* forces a zone removal and *none* lets the zones unchanged.
      # Be careful with the cache when changing this setting
      zones: 'global'
    layers: all
  # Datasheets downloader:
  - name: 'download_datasheets_example'
    comment: 'Downloads the datasheets for the project'
    type: 'download_datasheets'
    dir: 'Example/download_datasheets_dir'
    options:
      # [boolean=false] Use the reference to classify the components in different sub-dirs.
      # In this way C7 will go into a Capacitors sub-dir, R3 into Resistors, etc
      classify: false
      # [string_dict={}] Extra reference associations used to classify the references.
      # They are pairs `Reference prefix` -> `Sub-dir`
      classify_extra: {}
      # [boolean=false] Include the DNF components
      dnf: false
      # [string|list(string)='_null'] Name of the filter to mark components as not fitted.
      # Is a short-cut to use for simple cases where a variant is an overkill.
      # Can be used to fine-tune a variant for a particular output that needs extra filtering done before the
      # variant
      dnf_filter: '_null'
      # [string|list(string)='_null'] Name of the filter to exclude components from processing.
      # Is a short-cut to use for simple cases where a variant is an overkill.
      # Can be used to fine-tune a variant for a particular output that needs extra filtering done before the
      # variant
      exclude_filter: '_null'
      # [string='Datasheet'] Name of the field containing the URL
      field: 'Datasheet'
      # [boolean=true] Instead of download things we already downloaded use symlinks
      link_repeated: true
      # [string='${VALUE}.pdf'] Name used for the downloaded datasheet.
      # `${FIELD}` will be replaced by the FIELD content
      output: '${VALUE}.pdf'
      # [string|list(string)='_null'] Name of the filter to transform fields before applying other filters.
      # Is a short-cut to use for simple cases where a variant is an overkill.
      # Can be used to fine-tune a variant for a particular output that needs extra filtering done before the
      # variant
      pre_transform: '_null'
      # [boolean=false] Download URLs that we already downloaded.
      # It only makes sense if the `output` field makes their output different
      repeated: false
      # [string=''] Board variant to apply
      variant: ''
  # DXF (Drawing Exchange Format):
  # This output is what you get from the File/Plot menu in pcbnew.
  # Important: If you use custom fonts and/or colors please consult the `resources_dir` global variable.
  - name: 'dxf_example'
    comment: 'Exports the PCB to 2D mechanical EDA tools (like AutoCAD).'
    type: 'dxf'
    dir: 'Example/dxf_dir'
    options:
      # [list(dict)=[]] A list of customized reports for the manufacturer
      custom_reports:
        # [string=''] Content for the report. Use ``${basename}`` for the project name without extension.
        # Use ``${filename(LAYER)}`` for the file corresponding to LAYER
        - content: ''
          # [string='Custom_report.txt'] File name for the custom report
          output: 'Custom_report.txt'
      # [string|list(string)='_null'] Name of the filter to mark components as not fitted.
      # Is a short-cut to use for simple cases where a variant is an overkill.
      # Can be used to fine-tune a variant for a particular output that needs extra filtering done before the
      # variant
      dnf_filter: '_null'
      # [string='full'] [none,small,full] What to use to indicate the drill places, can be none, small or full (for real scale)
      drill_marks: 'full'
      # [string=''] Used to configure the edge cuts layer extension for Protel mode. Include the dot
      edge_cut_extension: ''
      # [boolean=true] Do not include the PCB edge layer
      exclude_edge_layer: true
      # [string|list(string)='_null'] Name of the filter to exclude components from processing.
      # Is a short-cut to use for simple cases where a variant is an overkill.
      # Can be used to fine-tune a variant for a particular output that needs extra filtering done before the
      # variant
      exclude_filter: '_null'
      # [boolean=false] Do not plot the component pads in the silk screen (KiCad 5.x only)
      exclude_pads_from_silkscreen: false
      # [boolean=false] Include references and values even when they are marked as invisible.
      # Not available on KiCad 9.0.1 and newer
      force_plot_invisible_refs_vals: false
      # [boolean=true] Tell KiCad to apply the scaling for each layer as a separated entity.
      # Disabling it the pages are coherent and can be superposed
      individual_page_scaling: true
      # [string=''] Used to change the Protel style extensions for inner layers.
      # The replacement pattern can contain %n for the inner layer number and %N for the layer number.
      # Example '.g%n'.
      # Important: this numbering is consistent and the first inner layer is %n = 1 and %N = 2. Which
      # isn't true for KiCad. KiCad 8 uses 2 for the first inner and KiCad 9 uses 1
      inner_extension_pattern: ''
      # [boolean=false] Use mm instead of inches
      metric_units: false
      # [string='%f-%i%I%v.%x'] Output file name, the default KiCad name if empty.
      # Important: KiCad will always create the file using its own name and then we can rename it.
      # For this reason you must avoid generating two variants at the same directory when one of
      # them uses the default KiCad name. Affected by global options
      output: '%f-%i%I%v.%x'
      # [boolean=true] Include the footprint references
      plot_footprint_refs: true
      # [boolean=true] Include the footprint values
      plot_footprint_values: true
      # [boolean=false] Include the frame and title block. Only available for KiCad 6+ and you get a poor result
      # (i.e. always the default worksheet style, also problems expanding text variables).
      # The `pcb_print` output can do a better job for PDF, SVG, PS, EPS and PNG outputs
      plot_sheet_reference: false
      # [boolean=true] Plot using the contour, instead of the center line.
      # You must disable it to get the dimensions (See https://gitlab.com/kicad/code/kicad/-/issues/11901)
      polygon_mode: true
      # [string|list(string)='_null'] Name of the filter to transform fields before applying other filters.
      # Is a short-cut to use for simple cases where a variant is an overkill.
      # Can be used to fine-tune a variant for a particular output that needs extra filtering done before the
      # variant
      pre_transform: '_null'
      # [number=1] Scale factor (0 means autoscaling)
      scaling: 1
      # [number=0.1] Line width for the sketched pads [mm], see `sketch_pads_on_fab_layers` (KiCad 6+)
      # Note that this value is currently ignored by KiCad (6.0.9)
      sketch_pad_line_width: 0.1
      # [boolean=false] Draw only the outline of the pads on the *.Fab layers (KiCad 6+)
      sketch_pads_on_fab_layers: false
      # [boolean=false] Don't fill objects, just draw the outline
      sketch_plot: false
      # [boolean=true] Cover the vias. Usable for KiCad versions older than 9.
      # Warning: KiCad 8 has a bug that ignores this option. Set it from KiCad GUI
      tent_vias: true
      # [boolean=false] Use uppercase names for the extensions
      uppercase_extensions: false
      # [boolean=false] Use the auxiliary axis as origin for coordinates
      use_aux_axis_as_origin: false
      # [string=''] Board variant to apply
      variant: ''
    layers: all
  # DXF Schematic Print (Drawing Exchange Format):
  # This output is what you get from the 'File/Plot' menu in eeschema.
  # Supports the image replacement using the prefix indicated by the `sch_image_prefix` global variable
  # Important: If you use custom fonts and/or colors please consult the `resources_dir` global variable.
  - name: 'dxf_sch_print_example'
    comment: 'Exports the schematic to a format commonly used for CAD software.'
    type: 'dxf_sch_print'
    dir: 'Example/dxf_sch_print_dir'
    options:
      # [boolean=true] Generate with all hierarchical sheets
      all_pages: true
      # [boolean=false] Use the background color from the `color_theme` (KiCad 6)
      background_color: false
      # [string=''] Color theme used, this must exist in the KiCad config (KiCad 6)
      color_theme: ''
      # [string='KiCad Font'] Name for the default font. Only for KiCad 9 and newer
      default_font: 'KiCad Font'
      # [string|list(string)='_null'] Name of the filter to mark components as not fitted.
      # Is a short-cut to use for simple cases where a variant is an overkill.
      # Can be used to fine-tune a variant for a particular output that needs extra filtering done before the
      # variant
      dnf_filter: '_null'
      # [string|list(string)='_null'] Name of the filter to exclude components from processing.
      # Is a short-cut to use for simple cases where a variant is an overkill.
      # Can be used to fine-tune a variant for a particular output that needs extra filtering done before the
      # variant
      exclude_filter: '_null'
      # [boolean=true] Include the frame and title block
      frame: true
      # [boolean=false] Generate a monochromatic output
      monochrome: false
      # [string='%f-%i%I%v.%x'] Filename for the output DXF (%i=schematic, %x=dxf). Affected by global options
      output: '%f-%i%I%v.%x'
      # [string|list(string)='_null'] Name of the filter to transform fields before applying other filters.
      # Is a short-cut to use for simple cases where a variant is an overkill.
      # Can be used to fine-tune a variant for a particular output that needs extra filtering done before the
      # variant
      pre_transform: '_null'
      # [string=''] Worksheet file (.kicad_wks) to use. Leave empty to use the one specified in the project.
      # This option works only when you print the toplevel sheet of a project and the project
      # file is available
      sheet_reference_layout: ''
      # [string=''] Text used to replace the sheet title. %VALUE expansions are allowed.
      # If it starts with `+` the text is concatenated
      title: ''
      # [string=''] Board variant to apply.
      # Not fitted components are crossed
      variant: ''
  # Excellon drill format:
  # You can create a map file for documentation purposes.
  # This output is what you get from the 'File/Fabrication output/Drill Files' menu in pcbnew.
  - name: 'excellon_example'
    comment: 'This is the main format for the drilling machine.'
    type: 'excellon'
    dir: 'Example/excellon_dir'
    options:
      # [string|list(string)='_null'] Name of the filter to mark components as not fitted.
      # Is a short-cut to use for simple cases where a variant is an overkill.
      # Can be used to fine-tune a variant for a particular output that needs extra filtering done before the
      # variant
      dnf_filter: '_null'
      # [string|list(string)='_null'] Name of the filter to exclude components from processing.
      # Is a short-cut to use for simple cases where a variant is an overkill.
      # Can be used to fine-tune a variant for a particular output that needs extra filtering done before the
      # variant
      exclude_filter: '_null'
      # [boolean=true] Generate drill files. Set to False and choose map format if only map is to be generated
      generate_drill_files: true
      # [number=0] number of digits for integer part of coordinates (0 is auto)
      left_digits: 0
      # [dict|string='None'] [hpgl,ps,gerber,dxf,svg,pdf,None] Format for a graphical drill map.
      # Not generated unless a format is specified
      map:
        # [string='%f-%i%I%v.%x'] Name for the map file, KiCad defaults if empty (%i='PTH_drill_map'). Affected by global options
        output: '%f-%i%I%v.%x'
        # [string='pdf'] [hpgl,ps,gerber,dxf,svg,pdf] Format for a graphical drill map
        type: 'pdf'
      # [boolean=true] Use metric units instead of inches
      metric_units: true
      # [boolean=false] Use a minimal header in the file
      minimal_header: false
      # [boolean=false] Invert the Y axis
      mirror_y_axis: false
      # [string] Force this replacement for %i when generating NPTH files
      npth_id: null
      # [string='%f-%i%I%v.%x'] name for the drill file, KiCad defaults if empty (%i='PTH_drill'). Affected by global options
      output: '%f-%i%I%v.%x'
      # [string|list(string)='_null'] Name of the filter to transform fields before applying other filters.
      # Is a short-cut to use for simple cases where a variant is an overkill.
      # Can be used to fine-tune a variant for a particular output that needs extra filtering done before the
      # variant
      pre_transform: '_null'
      # [boolean=true] Generate one file for both, plated holes and non-plated holes, instead of two separated files
      pth_and_npth_single_file: true
      # [string] Force this replacement for %i when generating PTH and unified files
      pth_id: null
      # [dict|string=''] Name of the drill report. Not generated unless a name is specified
      report:
        # [string=''] Name of the drill report. Not generated unless a name is specified.
        # (%i='drill_report' %x='txt')
        filename: ''
      # [number=0] number of digits for mantissa part of coordinates (0 is auto)
      right_digits: 0
      # [boolean=true] Use route command for oval holes (G00), otherwise use G85
      route_mode_for_oval_holes: true
      # [dict|string=''] Name of the drill table. Not generated unless a name is specified
      table:
        # [list(dict)|list(string)] List of columns to display.
        # Each entry can be a dictionary with `field`, `name` or just a string (field name)
        columns: ['Count', 'Hole Size', 'Plated', 'Hole Shape', 'Drill Layer Pair', 'Hole Type']
        # [boolean=true] By default KiCad groups slots and rounded holes if they can be cut from the same tool (same diameter)
        group_slots_and_round_holes: true
        # [string='%f-%i%I%v.%x'] Name of the drill table. Not generated unless a name is specified.
        # (%i='drill_table' %x='csv'). Affected by global options
        output: '%f-%i%I%v.%x'
        # [string='auto'] [yes,no,auto] Choose whether to unify plated and non-plated
        # holes in the same table. If 'auto' is chosen, the setting is copied
        # from the `excellon` output's `pth_and_npth_single_file`
        unify_pth_and_npth: 'auto'
        # [string='millimeters_mils'] [millimeters,mils,millimeters_mils,mils_millimeters] Units used for the hole sizes
        units: 'millimeters_mils'
      # [boolean=false] Use the auxiliary axis as origin for coordinates
      use_aux_axis_as_origin: false
      # [string=''] Board variant to apply.
      # Used for sub-PCBs
      variant: ''
      # [string='DECIMAL_FORMAT'] [DECIMAL_FORMAT,SUPPRESS_LEADING,SUPPRESS_TRAILING,KEEP_ZEROS] How to handle the zeros
      zeros_format: 'DECIMAL_FORMAT'
  # Various 3D models exports using KiCad (BREP/GLB/STL/STEP/XAO):
  # Supported formats include:
  # - STEP: ISO 10303-21 Clear Text Encoding of the Exchange Structure
  # - GLB: Binary version of the glTF, Graphics Library Transmission Format or GL Transmission Format and formerly
  #   known as WebGL Transmissions Format or WebGL TF.
  # - STL: 3D printer format, from stereolithography CAD software created by 3D Systems.
  # - XAO: XAO (SALOME/Gmsh) format, used for FEM and simulations.
  # - BRep: Part of Open CASCADE Technology (OCCT)
  # STEP is the most common 3D format for exchange purposes
  - name: 'export_3d_example'
    comment: 'Exports the PCB as a 3D model using KiCad 9 or newer.'
    type: 'export_3d'
    dir: 'Example/export_3d_dir'
    options:
      # [boolean=false] Only generate a board with no components
      board_only: false
      # [boolean=false] Cut via holes in board body even if conductor layers are not exported
      cut_vias_in_body: false
      # [string|list(string)='_null'] Name of the filter to mark components as not fitted.
      # Is a short-cut to use for simple cases where a variant is an overkill.
      # Can be used to fine-tune a variant for a particular output that needs extra filtering done before the
      # variant
      dnf_filter: '_null'
      # [boolean=true] Downloads missing 3D models from KiCad git.
      # Only applies to models in KISYS3DMOD and KICAD6_3DMODEL_DIR.
      # They are downloaded to a temporal directory and discarded.
      # If you want to cache the downloaded files specify a directory using the
      # KIBOT_3D_MODELS environment variable
      download: true
      # [boolean=true] In addition to try to download the 3D models from KiCad git also try to get
      # them from LCSC database. In order to work you'll need to provide the LCSC
      # part number. The field containing the LCSC part number is defined by the
      # `field_lcsc_part` global variable
      download_lcsc: true
      # [string|list(string)='_null'] Name of the filter to exclude components from processing.
      # Is a short-cut to use for simple cases where a variant is an overkill.
      # Can be used to fine-tune a variant for a particular output that needs extra filtering done before the
      # variant
      exclude_filter: '_null'
      # [boolean=false] Don't cut via holes in conductor layers
      fill_all_vias: false
      # [string='step'] [step,glb,stl,xao,brep] 3D format used.
      # - STEP: ISO 10303-21 Clear Text Encoding of the Exchange Structure
      # - GLB: Binary version of the glTF, Graphics Library Transmission Format or GL Transmission Format and formerly
      # known as WebGL Transmissions Format or WebGL TF.
      # - STL: 3D printer format, from stereolithography CAD software created by 3D Systems.
      # - XAO: XAO (SALOME/Gmsh) format, used for FEM and simulations.
      # - BRep: Part of Open CASCADE Technology (OCCT)
      format: 'step'
      # [boolean=false] Fuse overlapping geometry together
      fuse_shapes: false
      # [boolean=false] Export elements on inner copper layers
      include_inner_copper: false
      # [boolean=false] Export pads
      include_pads: false
      # [boolean=false] Export silkscreen graphics as a set of flat faces
      include_silkscreen: false
      # [boolean=false] Export soldermask layers as a set of flat faces
      include_soldermask: false
      # [boolean=false] Export tracks and vias
      include_tracks: false
      # [boolean=false] Export zones
      include_zones: false
      # [string='https://gitlab.com/kicad/libraries/kicad-packages3D/-/raw/master/'] Base URL for the KiCad 3D models
      kicad_3d_url: 'https://gitlab.com/kicad/libraries/kicad-packages3D/-/raw/master/'
      # [string=''] Text added to the end of the download URL.
      # Can be used to pass variables to the GET request, i.e. ?VAR1=VAL1&VAR2=VAL2
      kicad_3d_url_suffix: ''
      # [number=-1] The minimum distance between points to treat them as separate ones (-1 is KiCad default: 0.01 mm).
      # The units for this option are controlled by the `units` option
      min_distance: -1
      # [string=''] Only include copper items belonging to nets matching this wildcard
      net_filter: ''
      # [boolean=false] Exclude board body
      no_board_body: false
      # [boolean=false] Exclude 3D models for components
      no_components: false
      # [boolean=false] Do not optimize STEP file (enables writing parametric curves)
      no_optimize_step: false
      # [boolean=false] Used to exclude 3D models for components with 'virtual' attribute
      no_virtual: false
      # [string='grid'] [grid,drill,*] Determines the coordinates origin. Using grid the coordinates are the same as you have in the
      # design sheet.
      # The drill option uses the auxiliary reference defined by the user.
      # You can define any other origin using the format 'X,Y', i.e. '3.2,-10'. Don't put units here.
      # The units used here are the ones specified by the `units` option
      origin: 'grid'
      # [string='%f-%i%I%v.%x'] Name for the generated 3D file (%i='3D' %x='step/glb/stl/xao/brep'). Affected by global options
      output: '%f-%i%I%v.%x'
      # [string|list(string)='_null'] Name of the filter to transform fields before applying other filters.
      # Is a short-cut to use for simple cases where a variant is an overkill.
      # Can be used to fine-tune a variant for a particular output that needs extra filtering done before the
      # variant
      pre_transform: '_null'
      # [boolean=true] Substitute STEP or IGS models with the same name in place of VRML models
      subst_models: true
      # [string='millimeters'] [millimeters,inches,mils] Units used for the custom origin and `min_distance`. Affected by global options
      units: 'millimeters'
      # [string=''] Board variant to apply
      variant: ''
  # GenCAD:
  # This format is interpreted by some CADCAM software and helps certain
  # manufacturers
  - name: 'gencad_example'
    comment: 'Exports the PCB in GENCAD format.'
    type: 'gencad'
    dir: 'Example/gencad_dir'
    options:
      # [boolean=false] Use auxiliary axis as origin
      aux_origin: false
      # [string|list(string)='_null'] Name of the filter to mark components as not fitted.
      # Is a short-cut to use for simple cases where a variant is an overkill.
      # Can be used to fine-tune a variant for a particular output that needs extra filtering done before the
      # variant
      dnf_filter: '_null'
      # [string|list(string)='_null'] Name of the filter to exclude components from processing.
      # Is a short-cut to use for simple cases where a variant is an overkill.
      # Can be used to fine-tune a variant for a particular output that needs extra filtering done before the
      # variant
      exclude_filter: '_null'
      # [boolean=false] Flip bottom footprint padstacks
      flip_bottom_padstacks: false
      # [boolean=false] Generate a new shape for each footprint instance (Do not reuse shapes)
      no_reuse_shapes: false
      # [string='%f-%i%I%v.%x'] Filename for the output (%i=gencad, %x=cad). Affected by global options
      output: '%f-%i%I%v.%x'
      # [string|list(string)='_null'] Name of the filter to transform fields before applying other filters.
      # Is a short-cut to use for simple cases where a variant is an overkill.
      # Can be used to fine-tune a variant for a particular output that needs extra filtering done before the
      # variant
      pre_transform: '_null'
      # [boolean=false] Save the origin coordinates in the file
      save_origin: false
      # [boolean=false] Generate unique pin names
      unique_pin_names: false
      # [string=''] Board variant to apply.
      # Used for sub-PCBs
      variant: ''
  # Gerber drill format:
  # You can create a map file for documentation purposes.
  # This output is what you get from the 'File/Fabrication output/Drill Files' menu in pcbnew.
  - name: 'gerb_drill_example'
    comment: 'This is the information for the drilling machine in gerber format.'
    type: 'gerb_drill'
    dir: 'Example/gerb_drill_dir'
    options:
      # [string|list(string)='_null'] Name of the filter to mark components as not fitted.
      # Is a short-cut to use for simple cases where a variant is an overkill.
      # Can be used to fine-tune a variant for a particular output that needs extra filtering done before the
      # variant
      dnf_filter: '_null'
      # [string|list(string)='_null'] Name of the filter to exclude components from processing.
      # Is a short-cut to use for simple cases where a variant is an overkill.
      # Can be used to fine-tune a variant for a particular output that needs extra filtering done before the
      # variant
      exclude_filter: '_null'
      # [boolean=true] Generate drill files. Set to False and choose map format if only map is to be generated
      generate_drill_files: true
      # [dict|string='None'] [hpgl,ps,gerber,dxf,svg,pdf,None] Format for a graphical drill map.
      # Not generated unless a format is specified
      map:
        # [string='%f-%i%I%v.%x'] Name for the map file, KiCad defaults if empty (%i='PTH_drill_map'). Affected by global options
        output: '%f-%i%I%v.%x'
        # [string='pdf'] [hpgl,ps,gerber,dxf,svg,pdf] Format for a graphical drill map
        type: 'pdf'
      # [string] Force this replacement for %i when generating NPTH files
      npth_id: null
      # [string='%f-%i%I%v.%x'] name for the drill file, KiCad defaults if empty (%i='PTH_drill'). Affected by global options
      output: '%f-%i%I%v.%x'
      # [string|list(string)='_null'] Name of the filter to transform fields before applying other filters.
      # Is a short-cut to use for simple cases where a variant is an overkill.
      # Can be used to fine-tune a variant for a particular output that needs extra filtering done before the
      # variant
      pre_transform: '_null'
      # [string] Force this replacement for %i when generating PTH and unified files
      pth_id: null
      # [dict|string=''] Name of the drill report. Not generated unless a name is specified
      report:
        # [string=''] Name of the drill report. Not generated unless a name is specified.
        # (%i='drill_report' %x='txt')
        filename: ''
      # [dict|string=''] Name of the drill table. Not generated unless a name is specified
      table:
        # [list(dict)|list(string)] List of columns to display.
        # Each entry can be a dictionary with `field`, `name` or just a string (field name)
        columns: ['Count', 'Hole Size', 'Plated', 'Hole Shape', 'Drill Layer Pair', 'Hole Type']
        # [boolean=true] By default KiCad groups slots and rounded holes if they can be cut from the same tool (same diameter)
        group_slots_and_round_holes: true
        # [string='%f-%i%I%v.%x'] Name of the drill table. Not generated unless a name is specified.
        # (%i='drill_table' %x='csv'). Affected by global options
        output: '%f-%i%I%v.%x'
        # [string='auto'] [yes,no,auto] Choose whether to unify plated and non-plated
        # holes in the same table. If 'auto' is chosen, the setting is copied
        # from the `excellon` output's `pth_and_npth_single_file`
        unify_pth_and_npth: 'auto'
        # [string='millimeters_mils'] [millimeters,mils,millimeters_mils,mils_millimeters] Units used for the hole sizes
        units: 'millimeters_mils'
      # [boolean=false] Use the auxiliary axis as origin for coordinates
      use_aux_axis_as_origin: false
      # [string=''] Board variant to apply.
      # Used for sub-PCBs
      variant: ''
  # Gerber format:
  # This output is what you get from the File/Plot menu in pcbnew.
  # Important: If you use custom fonts and/or colors please consult the `resources_dir` global variable.
  - name: 'gerber_example'
    comment: 'This is the main fabrication format for the PCB.'
    type: 'gerber'
    dir: 'Example/gerber_dir'
    options:
      # [boolean=true] Creates a file with information about all the generated gerbers.
      # You can use it in gerbview to load all gerbers at once
      create_gerber_job_file: true
      # [list(dict)=[]] A list of customized reports for the manufacturer
      custom_reports:
        # [string=''] Content for the report. Use ``${basename}`` for the project name without extension.
        # Use ``${filename(LAYER)}`` for the file corresponding to LAYER
        - content: ''
          # [string='Custom_report.txt'] File name for the custom report
          output: 'Custom_report.txt'
      # [boolean=false] Disable aperture macros (workaround for buggy CAM software) (KiCad 6)
      disable_aperture_macros: false
      # [string|list(string)='_null'] Name of the filter to mark components as not fitted.
      # Is a short-cut to use for simple cases where a variant is an overkill.
      # Can be used to fine-tune a variant for a particular output that needs extra filtering done before the
      # variant
      dnf_filter: '_null'
      # [string=''] Used to configure the edge cuts layer extension for Protel mode. Include the dot
      edge_cut_extension: ''
      # [boolean=true] Do not include the PCB edge layer
      exclude_edge_layer: true
      # [string|list(string)='_null'] Name of the filter to exclude components from processing.
      # Is a short-cut to use for simple cases where a variant is an overkill.
      # Can be used to fine-tune a variant for a particular output that needs extra filtering done before the
      # variant
      exclude_filter: '_null'
      # [boolean=false] Do not plot the component pads in the silk screen (KiCad 5.x only)
      exclude_pads_from_silkscreen: false
      # [boolean=false] Include references and values even when they are marked as invisible.
      # Not available on KiCad 9.0.1 and newer
      force_plot_invisible_refs_vals: false
      # [string='%f-%i%I%v.%x'] Name for the gerber job file (%i='job', %x='gbrjob'). Affected by global options
      gerber_job_file: '%f-%i%I%v.%x'
      # [number=4.6] [4.5;4.6] This is the gerber coordinate format, can be 4.5 or 4.6
      gerber_precision: 4.6
      # [string=''] Used to change the Protel style extensions for inner layers.
      # The replacement pattern can contain %n for the inner layer number and %N for the layer number.
      # Example '.g%n'.
      # Important: this numbering is consistent and the first inner layer is %n = 1 and %N = 2. Which
      # isn't true for KiCad. KiCad 8 uses 2 for the first inner and KiCad 9 uses 1
      inner_extension_pattern: ''
      # [number=0.1] [0.02,2] Line_width for objects without width [mm] (KiCad 5)
      line_width: 0.1
      # [string='%f-%i%I%v.%x'] Output file name, the default KiCad name if empty.
      # Important: KiCad will always create the file using its own name and then we can rename it.
      # For this reason you must avoid generating two variants at the same directory when one of
      # them uses the default KiCad name. Affected by global options
      output: '%f-%i%I%v.%x'
      # [boolean=true] Include the footprint references
      plot_footprint_refs: true
      # [boolean=true] Include the footprint values
      plot_footprint_values: true
      # [boolean=false] Include the frame and title block. Only available for KiCad 6+ and you get a poor result
      # (i.e. always the default worksheet style, also problems expanding text variables).
      # The `pcb_print` output can do a better job for PDF, SVG, PS, EPS and PNG outputs
      plot_sheet_reference: false
      # [string|list(string)='_null'] Name of the filter to transform fields before applying other filters.
      # Is a short-cut to use for simple cases where a variant is an overkill.
      # Can be used to fine-tune a variant for a particular output that needs extra filtering done before the
      # variant
      pre_transform: '_null'
      # [number=0.1] Line width for the sketched pads [mm], see `sketch_pads_on_fab_layers` (KiCad 6+)
      # Note that this value is currently ignored by KiCad (6.0.9)
      sketch_pad_line_width: 0.1
      # [boolean=false] Draw only the outline of the pads on the *.Fab layers (KiCad 6+)
      sketch_pads_on_fab_layers: false
      # [boolean=false] Subtract the solder mask from the silk screen
      subtract_mask_from_silk: false
      # [boolean=true] Cover the vias. Usable for KiCad versions older than 9.
      # Warning: KiCad 8 has a bug that ignores this option. Set it from KiCad GUI
      tent_vias: true
      # [boolean=false] Use uppercase names for the extensions
      uppercase_extensions: false
      # [boolean=false] Use the auxiliary axis as origin for coordinates
      use_aux_axis_as_origin: false
      # [boolean=true] Include netlist metadata
      use_gerber_net_attributes: true
      # [boolean=true] Use the extended X2 format (otherwise use X1 formerly RS-274X)
      use_gerber_x2_attributes: true
      # [boolean=false] Use legacy Protel file extensions.
      # Important: Inner layers numbering is different for KiCad 8 and 9. KiCad 8 starts numbering inner
      # layers with 2 and KiCad 9 with 1
      use_protel_extensions: false
      # [string=''] Board variant to apply
      variant: ''
    layers: all
  # HPGL (Hewlett & Packard Graphics Language):
  # This output is what you get from the File/Plot menu in pcbnew.
  # Important: If you use custom fonts and/or colors please consult the `resources_dir` global variable.
  - name: 'hpgl_example'
    comment: 'Exports the PCB for plotters and laser printers.'
    type: 'hpgl'
    dir: 'Example/hpgl_dir'
    options:
      # [list(dict)=[]] A list of customized reports for the manufacturer
      custom_reports:
        # [string=''] Content for the report. Use ``${basename}`` for the project name without extension.
        # Use ``${filename(LAYER)}`` for the file corresponding to LAYER
        - content: ''
          # [string='Custom_report.txt'] File name for the custom report
          output: 'Custom_report.txt'
      # [string|list(string)='_null'] Name of the filter to mark components as not fitted.
      # Is a short-cut to use for simple cases where a variant is an overkill.
      # Can be used to fine-tune a variant for a particular output that needs extra filtering done before the
      # variant
      dnf_filter: '_null'
      # [string='full'] [none,small,full] What to use to indicate the drill places, can be none, small or full (for real scale)
      drill_marks: 'full'
      # [string=''] Used to configure the edge cuts layer extension for Protel mode. Include the dot
      edge_cut_extension: ''
      # [boolean=true] Do not include the PCB edge layer
      exclude_edge_layer: true
      # [string|list(string)='_null'] Name of the filter to exclude components from processing.
      # Is a short-cut to use for simple cases where a variant is an overkill.
      # Can be used to fine-tune a variant for a particular output that needs extra filtering done before the
      # variant
      exclude_filter: '_null'
      # [boolean=false] Do not plot the component pads in the silk screen (KiCad 5.x only)
      exclude_pads_from_silkscreen: false
      # [boolean=false] Include references and values even when they are marked as invisible.
      # Not available on KiCad 9.0.1 and newer
      force_plot_invisible_refs_vals: false
      # [boolean=true] Tell KiCad to apply the scaling for each layer as a separated entity.
      # Disabling it the pages are coherent and can be superposed
      individual_page_scaling: true
      # [string=''] Used to change the Protel style extensions for inner layers.
      # The replacement pattern can contain %n for the inner layer number and %N for the layer number.
      # Example '.g%n'.
      # Important: this numbering is consistent and the first inner layer is %n = 1 and %N = 2. Which
      # isn't true for KiCad. KiCad 8 uses 2 for the first inner and KiCad 9 uses 1
      inner_extension_pattern: ''
      # [boolean=false] Plot mirrored
      mirror_plot: false
      # [string='%f-%i%I%v.%x'] Output file name, the default KiCad name if empty.
      # Important: KiCad will always create the file using its own name and then we can rename it.
      # For this reason you must avoid generating two variants at the same directory when one of
      # them uses the default KiCad name. Affected by global options
      output: '%f-%i%I%v.%x'
      # [number=1] [1,16] Pen number
      pen_number: 1
      # [number=20] [1,99] Pen speed
      pen_speed: 20
      # [number=15] [0,100] Pen diameter in MILS, useful to fill areas. However, it is in mm in HPGL files
      pen_width: 15
      # [boolean=true] Include the footprint references
      plot_footprint_refs: true
      # [boolean=true] Include the footprint values
      plot_footprint_values: true
      # [boolean=false] Include the frame and title block. Only available for KiCad 6+ and you get a poor result
      # (i.e. always the default worksheet style, also problems expanding text variables).
      # The `pcb_print` output can do a better job for PDF, SVG, PS, EPS and PNG outputs
      plot_sheet_reference: false
      # [string|list(string)='_null'] Name of the filter to transform fields before applying other filters.
      # Is a short-cut to use for simple cases where a variant is an overkill.
      # Can be used to fine-tune a variant for a particular output that needs extra filtering done before the
      # variant
      pre_transform: '_null'
      # [number=0] Scale factor (0 means autoscaling)
      scaling: 0
      # [number=0.1] Line width for the sketched pads [mm], see `sketch_pads_on_fab_layers` (KiCad 6+)
      # Note that this value is currently ignored by KiCad (6.0.9)
      sketch_pad_line_width: 0.1
      # [boolean=false] Draw only the outline of the pads on the *.Fab layers (KiCad 6+)
      sketch_pads_on_fab_layers: false
      # [boolean=false] Don't fill objects, just draw the outline
      sketch_plot: false
      # [boolean=true] Cover the vias. Usable for KiCad versions older than 9.
      # Warning: KiCad 8 has a bug that ignores this option. Set it from KiCad GUI
      tent_vias: true
      # [boolean=false] Use uppercase names for the extensions
      uppercase_extensions: false
      # [string=''] Board variant to apply
      variant: ''
    layers: all
  # HPGL Schematic Print (Hewlett & Packard Graphics Language):
  # This output is what you get from the 'File/Plot' menu in eeschema.
  # Supports the image replacement using the prefix indicated by the `sch_image_prefix` global variable
  # Important: If you use custom fonts and/or colors please consult the `resources_dir` global variable.
  - name: 'hpgl_sch_print_example'
    comment: 'Exports the schematic to the most common plotter format.'
    type: 'hpgl_sch_print'
    dir: 'Example/hpgl_sch_print_dir'
    options:
      # [boolean=true] Generate with all hierarchical sheets
      all_pages: true
      # [boolean=false] Use the background color from the `color_theme` (KiCad 6)
      background_color: false
      # [string=''] Color theme used, this must exist in the KiCad config (KiCad 6)
      color_theme: ''
      # [string='KiCad Font'] Name for the default font. Only for KiCad 9 and newer
      default_font: 'KiCad Font'
      # [string|list(string)='_null'] Name of the filter to mark components as not fitted.
      # Is a short-cut to use for simple cases where a variant is an overkill.
      # Can be used to fine-tune a variant for a particular output that needs extra filtering done before the
      # variant
      dnf_filter: '_null'
      # [string|list(string)='_null'] Name of the filter to exclude components from processing.
      # Is a short-cut to use for simple cases where a variant is an overkill.
      # Can be used to fine-tune a variant for a particular output that needs extra filtering done before the
      # variant
      exclude_filter: '_null'
      # [boolean=true] Include the frame and title block
      frame: true
      # [boolean=false] Generate a monochromatic output
      monochrome: false
      # [string='bottom_left'] [bottom_left,centered,page_fit,content_fit] Origin and scale
      origin: 'bottom_left'
      # [string='%f-%i%I%v.%x'] Filename for the output HPGL (%i=schematic, %x=plt). Affected by global options
      output: '%f-%i%I%v.%x'
      # [number=0.4826] Pen size (diameter) [mm]
      pen_size: 0.4826
      # [string|list(string)='_null'] Name of the filter to transform fields before applying other filters.
      # Is a short-cut to use for simple cases where a variant is an overkill.
      # Can be used to fine-tune a variant for a particular output that needs extra filtering done before the
      # variant
      pre_transform: '_null'
      # [string=''] Worksheet file (.kicad_wks) to use. Leave empty to use the one specified in the project.
      # This option works only when you print the toplevel sheet of a project and the project
      # file is available
      sheet_reference_layout: ''
      # [string=''] Text used to replace the sheet title. %VALUE expansions are allowed.
      # If it starts with `+` the text is concatenated
      title: ''
      # [string=''] Board variant to apply.
      # Not fitted components are crossed
      variant: ''
  # IBoM (Interactive HTML BoM):
  # For more information: https://github.com/INTI-CMNB/InteractiveHtmlBom
  # This output is what you get from the InteractiveHtmlBom plug-in (pcbnew).
  - name: 'ibom_example'
    comment: 'Generates an interactive web page useful to identify the position of the components in the PCB.'
    type: 'ibom'
    dir: 'Example/ibom_dir'
    options:
      # [string=''] List of comma separated blacklisted components or prefixes with *. E.g. 'X1,MH*'.
      # IBoM option, avoid using in conjunction with KiBot variants/filters
      blacklist: ''
      # [boolean=false] Blacklist components with empty value.
      # IBoM option, avoid using in conjunction with KiBot variants/filters
      blacklist_empty_val: false
      # [number=0] Board rotation in degrees (-180 to 180). Will be rounded to multiple of 5
      board_rotation: 0
      # [string='left-right'] [bom-only,left-right,top-bottom] Default BOM view
      bom_view: 'left-right'
      # [string='Sourced,Placed'] Comma separated list of checkbox columns
      checkboxes: 'Sourced,Placed'
      # [boolean=false] Default to dark mode
      dark_mode: false
      # [string|list(string)='_null'] Name of the filter to mark components as not fitted.
      # Is a short-cut to use for simple cases where a variant is an overkill.
      # Can be used to fine-tune a variant for a particular output that needs extra filtering done before the
      # variant.
      # Avoid using it in conjunction with IBoM native filtering options
      dnf_filter: '_null'
      # [string=''] Name of the extra field that indicates do not populate status.
      # Components with this field not empty will be blacklisted.
      # IBoM option, avoid using in conjunction with KiBot variants/filters
      dnp_field: ''
      # [string|list(string)='_null'] Name of the filter to exclude components from processing.
      # Is a short-cut to use for simple cases where a variant is an overkill.
      # Can be used to fine-tune a variant for a particular output that needs extra filtering done before the
      # variant
      exclude_filter: '_null'
      # [string=''] Path to netlist or xml file. You can use '%F.xml' to avoid specifying the project name.
      # Leave it blank for most uses, data will be extracted from the PCB
      extra_data_file: ''
      # [string=''] Comma separated list of extra fields to pull from netlist or xml file.
      # Using 'X,Y' is a shortcut for `show_fields` and `group_fields` with values 'Value,Footprint,X,Y'
      extra_fields: ''
      # [string=''] Name to be used for the PCB/project (no file extension).
      # This will affect the name iBoM displays in the generated HTML
      forced_name: ''
      # [string=''] Comma separated list of fields that components will be grouped by.
      # Value and Footprint are used when nothing is specified
      group_fields: ''
      # [boolean=false] Hide components in the Fab layer that are marked as excluded by a variant.
      # Affected by global options
      hide_excluded: false
      # [boolean=false] Hide footprint pads by default
      hide_pads: false
      # [boolean=false] Hide silkscreen by default
      hide_silkscreen: false
      # [boolean|string=false] [none,all,selected] Highlight pin1 by default
      highlight_pin1: false
      # [boolean=false] Include netlist information in output.
      include_nets: false
      # [boolean=false] Include track/zone information in output. F.Cu and B.Cu layers only
      include_tracks: false
      # [string='FB'] [F,FB,B] Default layer view
      layer_view: 'FB'
      # [string='ibom'] Output file name format supports substitutions:
      # %f : original pcb file name without extension.
      # %p : pcb/project title from pcb metadata.
      # %c : company from pcb metadata.
      # %r : revision from pcb metadata.
      # %d : pcb date from metadata if available, file modification date otherwise.
      # %D : bom generation date.
      # %T : bom generation time.
      # Extension .html will be added automatically.
      # Note that this name is used only when output is ''
      name_format: 'ibom'
      # `netlist_file` is an alias for `extra_data_file`
      # [boolean=false] Do not blacklist virtual components.
      # IBoM option, avoid using in conjunction with KiBot variants/filters
      no_blacklist_virtual: false
      # [boolean=false] Disable compression of pcb data
      no_compression: false
      # [boolean=false] Do not redraw pcb on drag by default
      no_redraw_on_drag: false
      # [boolean=false] Normalize extra field name case. E.g. 'MPN' and 'mpn' will be considered the same field
      normalize_field_case: false
      # [boolean=false] Offset the back of the pcb by 180 degrees
      offset_back_rotation: false
      # [string='%f-%i%I%v.%x'] Filename for the output, use '' to use the IBoM filename (%i=ibom, %x=html). Affected by global options
      output: '%f-%i%I%v.%x'
      # [string|list(string)='_null'] Name of the filter to transform fields before applying other filters.
      # Is a short-cut to use for simple cases where a variant is an overkill.
      # Can be used to fine-tune a variant for a particular output that needs extra filtering done before the
      # variant
      pre_transform: '_null'
      # [boolean=false] Show fabrication layer by default
      show_fabrication: false
      # [string=''] Comma separated list of fields to show in the BOM.
      # Value and Footprint are displayed when nothing is specified
      show_fields: ''
      # [string='C,R,L,D,U,Y,X,F,SW,A,~,HS,CNN,J,P,NT,MH'] Default sort order for components. Must contain '~' once
      sort_order: 'C,R,L,D,U,Y,X,F,SW,A,~,HS,CNN,J,P,NT,MH'
      # [string=''] Board variant to apply.
      # Avoid using it in conjunction with IBoM native filtering options
      variant: ''
      # [string=''] Name of the extra field that stores board variant for component.
      # IBoM option, avoid using in conjunction with KiBot variants/filters
      variant_field: ''
      # [string=''] List of board variants to exclude from the BOM.
      # IBoM option, avoid using in conjunction with KiBot variants/filters
      variants_blacklist: ''
      # [string=''] List of board variants to include in the BOM.
      # IBoM option, avoid using in conjunction with KiBot variants/filters
      variants_whitelist: ''
  # Info:
  # It can be used to know more about the environment used to generate the files.
  # Please don't rely on the way things are reported, its content could change,
  # adding or removing information
  - name: 'info_example'
    comment: 'Records information about the current run.'
    type: 'info'
    dir: 'Example/info_dir'
    options:
      # [string='names'] [names,none,full] List environment variables.
      # IMPORTANT: Don't use `full` unless you know you are not leaking sensitive information
      environment: 'names'
      # [string='%f-%i%I%v.%x'] Filename for the output (%i=info, %x=txt). Affected by global options
      output: '%f-%i%I%v.%x'
  # IPC-DPMX (IPC-2581):
  # Only available for KiCad 9 and newer.
  # The requested fields are optional
  - name: 'ipc2581_example'
    comment: 'Exports the PCB in the Digital Product Model Exchange IPC format.'
    type: 'ipc2581'
    dir: 'Example/ipc2581_dir'
    options:
      # [boolean=true] Compress the XML file as a *zip* file
      compress: true
      # [string|list(string)='_null'] Name of the filter to mark components as not fitted.
      # Is a short-cut to use for simple cases where a variant is an overkill.
      # Can be used to fine-tune a variant for a particular output that needs extra filtering done before the
      # variant
      dnf_filter: '_null'
      # [string|list(string)='_null'] Name of the filter to exclude components from processing.
      # Is a short-cut to use for simple cases where a variant is an overkill.
      # Can be used to fine-tune a variant for a particular output that needs extra filtering done before the
      # variant
      exclude_filter: '_null'
      # [string='_field_dist_part_number'] Name of the field used for the distributor part number.
      # Use the `field_dist_part_number` global variable to define `_field_dist_part_number`
      field_dist_part_number: '_field_dist_part_number'
      # [string='_field_distributor'] Name of the field used for the distributor.
      # Use the `field_distributor` global variable to define `_field_distributor`
      field_distributor: '_field_distributor'
      # [string=''] Name of the field used as an internal ID.
      # Leave empty to create unique IDs
      field_internal_id: ''
      # [string='_field_manufacturer'] Name of the field used for the manufacturer.
      # Use the `field_manufacturer` global variable to define `_field_manufacturer`
      field_manufacturer: '_field_manufacturer'
      # [string='_field_part_number'] Name of the field used for the manufacturer part number.
      # Use the `field_part_number` global variable to define `_field_part_number`
      field_part_number: '_field_part_number'
      # [string='%f-%i%I%v.%x'] Filename for the output (%i=IPC-2581, %x=zip/xml)
      # The extension depends on the compress option. Affected by global options
      output: '%f-%i%I%v.%x'
      # [string|list(string)='_null'] Name of the filter to transform fields before applying other filters.
      # Is a short-cut to use for simple cases where a variant is an overkill.
      # Can be used to fine-tune a variant for a particular output that needs extra filtering done before the
      # variant
      pre_transform: '_null'
      # [number=6] Number of decimals used to represent the values
      precision: 6
      # [string='millimeters'] [millimeters,inches] Units used for the positions. Affected by global options.
      # Note that when using *mils* as global units this option becomes *inches*
      units: 'millimeters'
      # [string=''] Board variant to apply
      variant: ''
      # [string='C'] [B,C] Which implementation of the IPC-2581 standard will be generated
      version: 'C'
  # KiCad Jobset (batch execution):
  # The outputs will be generated using the `dir` directory as base.
  # This is provided just for convenience
  - name: 'jobset_example'
    comment: 'Generates outputs defined in a KiCad jobset file (.kicad_jobset).'
    type: 'jobset'
    dir: 'Example/jobset_dir'
    options:
      # [string|list(string)='_null'] Name of the filter to mark components as not fitted.
      # Is a short-cut to use for simple cases where a variant is an overkill.
      # Can be used to fine-tune a variant for a particular output that needs extra filtering done before the
      # variant
      dnf_filter: '_null'
      # [boolean=true] Downloads missing 3D models from KiCad git.
      # Only applies to models in KISYS3DMOD and KICAD6_3DMODEL_DIR.
      # They are downloaded to a temporal directory and discarded.
      # If you want to cache the downloaded files specify a directory using the
      # KIBOT_3D_MODELS environment variable
      download: true
      # [boolean=true] In addition to try to download the 3D models from KiCad git also try to get
      # them from LCSC database. In order to work you'll need to provide the LCSC
      # part number. The field containing the LCSC part number is defined by the
      # `field_lcsc_part` global variable
      download_lcsc: true
      # [string|list(string)='_null'] Name of the filter to exclude components from processing.
      # Is a short-cut to use for simple cases where a variant is an overkill.
      # Can be used to fine-tune a variant for a particular output that needs extra filtering done before the
      # variant
      exclude_filter: '_null'
      # [string=''] Name of the KiCad jobset file you want to use. Should have `kicad_jobset` extension.
      # Leave empty to look for a jobset with the same name as the project
      jobset: ''
      # [string='https://gitlab.com/kicad/libraries/kicad-packages3D/-/raw/master/'] Base URL for the KiCad 3D models
      kicad_3d_url: 'https://gitlab.com/kicad/libraries/kicad-packages3D/-/raw/master/'
      # [string=''] Text added to the end of the download URL.
      # Can be used to pass variables to the GET request, i.e. ?VAR1=VAL1&VAR2=VAL2
      kicad_3d_url_suffix: ''
      # [boolean=false] Used to exclude 3D models for components with 'virtual' attribute
      no_virtual: false
      # [string|list(string)='_null'] Name of the filter to transform fields before applying other filters.
      # Is a short-cut to use for simple cases where a variant is an overkill.
      # Can be used to fine-tune a variant for a particular output that needs extra filtering done before the
      # variant
      pre_transform: '_null'
      # [string=''] Output to be generated. When empty KiCad runs all possible outputs.
      # Here the name can be obtained from the .kicad_jobset file, in JSON format.
      # The `outputs` section contains all the defined outputs. Each output has an `id` use it here
      run_output: ''
      # [boolean=true] Stop generation when an error is detected
      stop_on_error: true
      # [string=''] Board variant to apply
      variant: ''
  # KiBoM (KiCad Bill of Materials):
  # For more information: https://github.com/INTI-CMNB/KiBoM
  # Note that this output is provided as a compatibility tool.
  # We recommend using the `bom` output instead.
  # This output is what you get from the 'Tools/Generate Bill of Materials' menu in eeschema.
  # Also note that here the KiBot concept of variants doesn't apply.
  - name: 'kibom_example'
    comment: 'Used to generate the BoM in HTML or CSV format using the KiBoM plug-in.'
    type: 'kibom'
    dir: 'Example/kibom_dir'
    options:
      # [string|dict='bom.ini'] BoM configuration file, relative to PCB. Environment variables and ~ allowed.
      # You can also define the configuration here, will be stored in `config.kibom.ini`
      conf:
        # [list(dict)|list(string)=[]] List of columns to display.
        # Can be just the name of the field
        columns:
          # [string=''] Name of the field to use for this column.
          # Use `_field_lcsc_part` to get the value defined in the global options
          - field: 'Row'
            # [list(string)|string=''] List of fields to join to this column
            join: ''
            # [string=''] Name to display in the header. The field is used when empty
            name: 'Line'
        # [list(list(string))] A series of values which are considered to be equivalent for the part name.
        # Each entry is a list of equivalen names. Example: ['c', 'c_small', 'cap' ]
        # will ensure the equivalent capacitor symbols can be grouped together.
        # If empty the following aliases are used:
        # - ['r', 'r_small', 'res', 'resistor']
        # - ['l', 'l_small', 'inductor']
        # - ['c', 'c_small', 'cap', 'capacitor']
        # - ['sw', 'switch']
        # - ['zener', 'zenersmall']
        # - ['d', 'diode', 'd_small']
        component_aliases: [['r', 'r_small', 'res', 'resistor'], ['l', 'l_small', 'inductor'], ['c', 'c_small', 'cap', 'capacitor'], ['sw', 'switch'], ['zener', 'zenersmall'], ['d', 'diode', 'd_small']]
        # [string=''] Column with links to the datasheet (HTML only)
        datasheet_as_link: ''
        # [string|list(string)=''] Column/s containing Digi-Key part numbers, will be linked to web page (HTML only)
        digikey_link: ''
        # [list(dict)=[]] A series of regular expressions used to exclude parts.
        # If a component matches ANY of these, it will be excluded.
        # Column names are case-insensitive.
        # If empty the following list is used by KiBoM:
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
